mmosko/Zx50/boards/Zx50_MemoryCard_RevC1/.kinotes/KiNotes_Zx50_MemoryCard_RevC.md

# **Zx50_MemoryCard_RevC - Design Notes**

## **Overview**
<!-- Brief description of the PCB project -->

## **Schematic Notes**
<!-- Key circuit blocks, design rationale -->

## **Layout Considerations**
<!-- Layer stackup, impedance, keep-outs -->

## **Component Notes**
<!-- Click on designators like R1, C5, U3 to highlight on PCB -->

## **Power Distribution**
<!-- Power rails, decoupling strategy -->

## **Signal Integrity**
<!-- Critical nets, routing constraints -->

## **References**
<!-- Datasheets, application notes, calculations -->

---
*KiNotes - PCBtools.xyz*
