mmosko/Zx50/firmware/BusProbe_RevB/Zx50_Bus_Probe.X/STATUS.md

This is a perfect place to take a break. You have fought through some of the most notorious legacy bugs in the MPLAB X Simulator today and successfully built a robust, testable firmware architecture. 

Here is a summary of exactly where we are so you can jump right back in next time without missing a beat.

### 🌟 What is Working Perfectly
* **The Simulator Bypass:** We abandoned the buggy external SCL scripts in favor of a C-level `#ifdef __DEBUG` mock array in `UART_Read()`. This reliably instantly feeds your 5-byte packets (SYNC, OPCODE, ADDR_H, ADDR_L, PARAM) into the state machine.
* **The Command Router:** Your `while(1)` loop and `switch(opcode)` block in `main.c` perfectly parse the mock packets and route them to the correct functions.
* **Safe Boot State:** We updated `GPIO_Init()` to pre-load `LATA` and `LATB` to `1` (HIGH) before setting their `TRIS` directions. This ensures the Z80 control lines and transceiver Output Enables (`~OE`) boot up safely disabled (Ghost Mode) without glitching the bus.
* **Ghost/Unghost Logic:** The new `CMD_GHOST` (0x08) command and `Ghost()` function successfully toggle the data bus direction (`TRISD`) and transceiver `~OE` lines (`RA0`, `RA2`). You can see this clearly working in your latest Logic Analyzer trace.
* **UART ACKs:** We verified via the IO View that the hardware is correctly loading `0x5A` into `TXREG` and enabling the transmission shift register after every command.

### 🔍 Where to Resume Next Session
Looking at your final screenshot, `RA0` and `RA2` are correctly cycling, but **`RB0` (`~MREQ`) and `RB5` (`~WR`) are sitting flat at 5V** during the entire trace. 

Since we pre-loaded them to 5V in `hal.c`, they are behaving safely, but they aren't dropping low to actually strobe the Z80 bus during the `CMD_STORE` operation. 

**Your To-Do List for next time:**
1.  **Open `z80_bus.c`:** Check your `Z80_Mem_Write()` function. We need to ensure it is actually pulling `LATBbits.LATB0 = 0` and `LATBbits.LATB5 = 0`, holding them for a moment, and then returning them to `1`.
2.  **Test a Read Command:** Once the write strobes are fixed, we will change the mock array in `hal.c` to inject a `CMD_LD` (Memory Read) packet. This will let us verify that your Transceiver Direction pins (`RA1`, `RA3`) correctly flip to route data *inward* from the Z80 bus.
3.  **Physical Hardware:** Once those last few logic lines are verified, the firmware is fully simulated. You can switch to VS Code, flash the physical PIC, and hook up your logic analyzer to the real PCB!

Have a great break. Whenever you are ready to pick this back up, just say the word!
