mmosko/Zx50/boards/Zx50_Clock_Mezzanine/Zx50_Clock_Mezzanine.kicad_pcb

## KiCad design boards/legacy/Zx50_Clock_Mezzanine/Zx50_Clock_Mezzanine.kicad_pcb (2026-03-17, an earlier design)

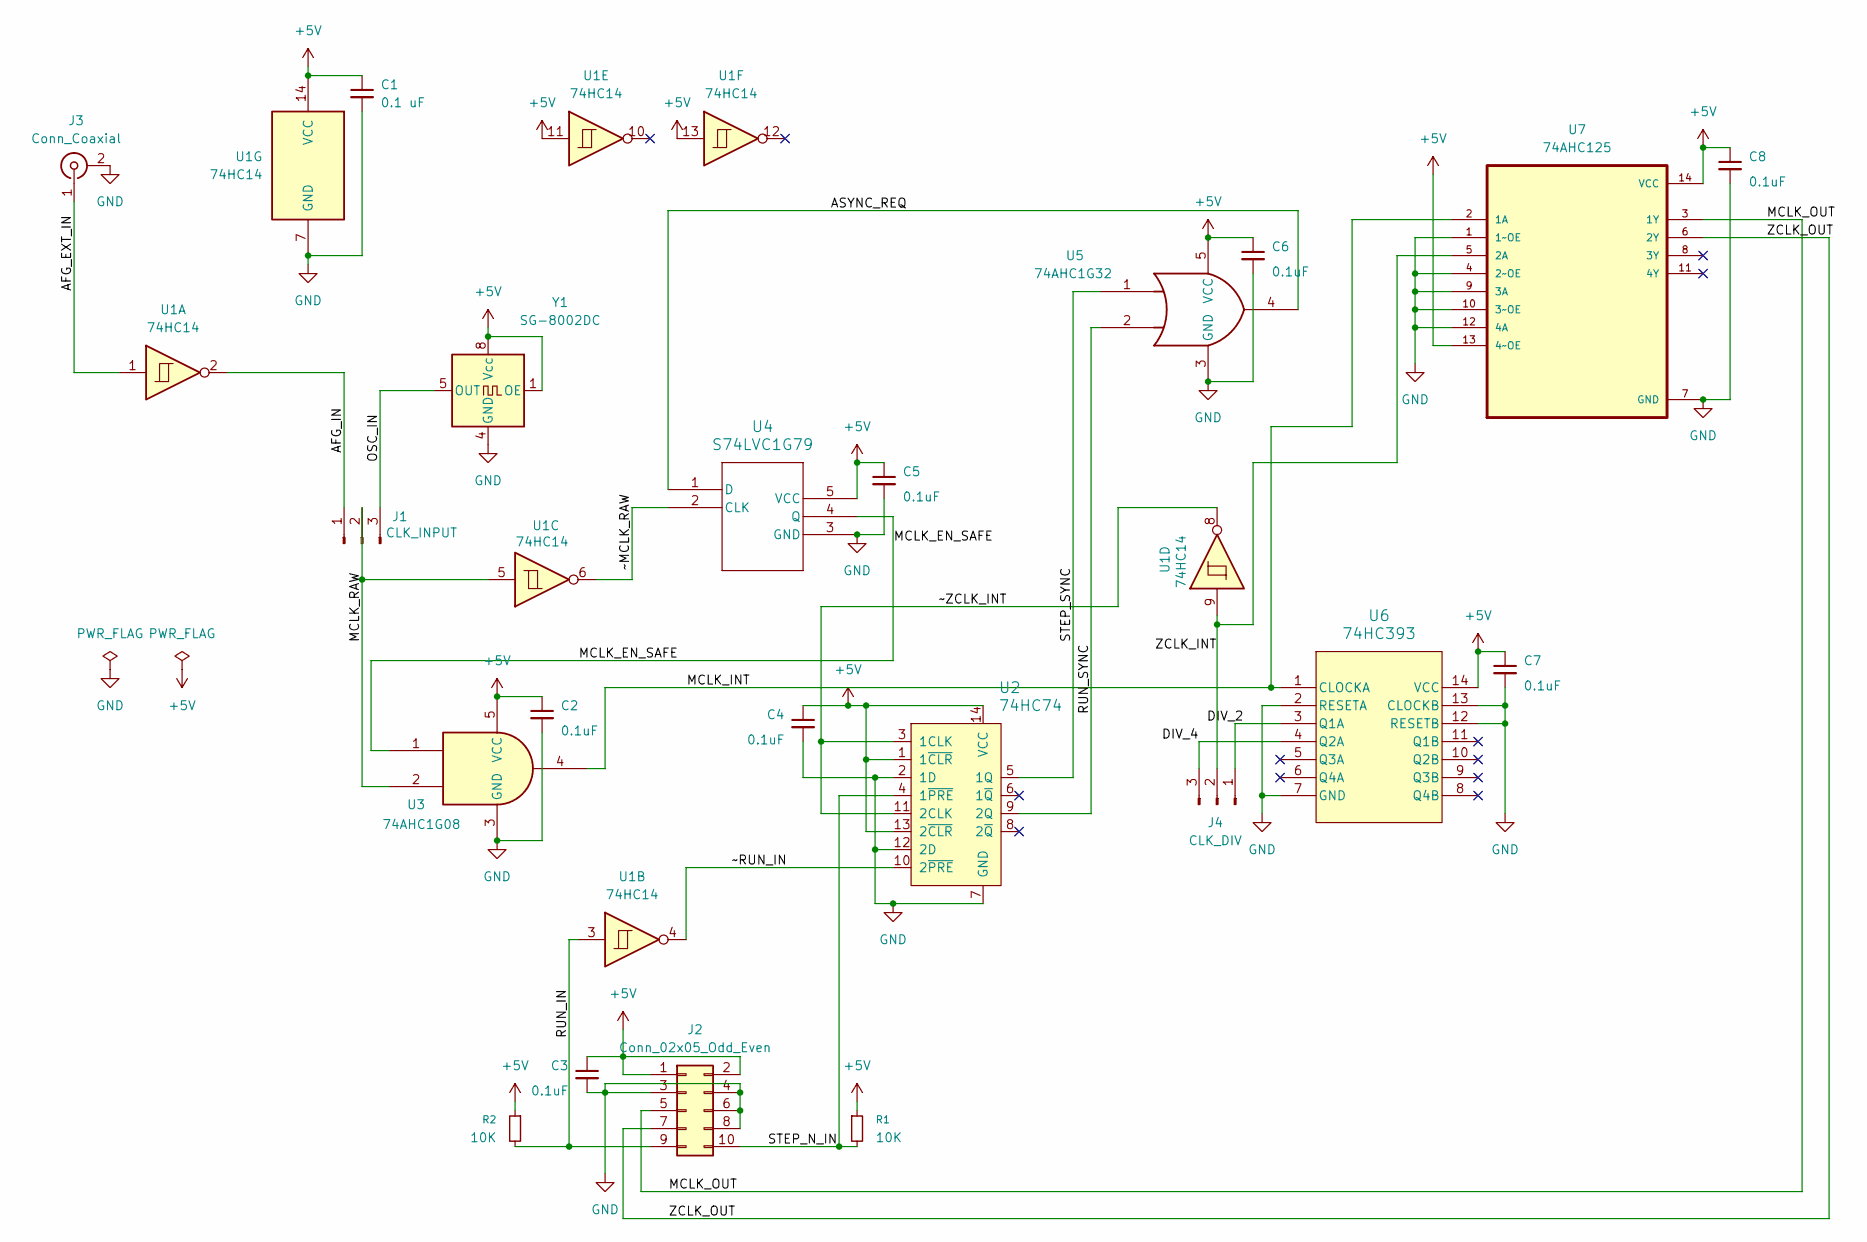
[picture p43: schematic Zx50_Clock_Mezzanine.kicad_sch]

Parts:
C1: 0.1 uF; C_0805_2012Metric_Pad1.18x1.45mm_HandSolder; DigiKey_PN 311-1140-1-ND
C2, C3, C4, C5, C6, C7, C8: 0.1uF; C_0805_2012Metric_Pad1.18x1.45mm_HandSolder; DigiKey_PN 311-1140-1-ND
J1: CLK_INPUT; PinHeader_1x03_P2.54mm_Vertical; DigiKey_PN 732-5316-ND
J2: Conn_02x05_Odd_Even; PinHeader_2x05_P2.54mm_Vertical; DigiKey_PN 2057-PH2RA-10-UA-ND
J3: Conn_Coaxial; BNC_Amphenol_B6252HB-NPP3G-50_Horizontal; DigiKey_PN ARF1178-ND
J4: CLK_DIV; PinHeader_1x03_P2.54mm_Vertical; DigiKey_PN 732-5316-ND
R1, R2: 10K; R_0805_2012Metric_Pad1.20x1.40mm_HandSolder; DigiKey_PN 311-10.0KCRCT-ND
U1: 74HC14; SOIC-14_3.9x8.7mm_P1.27mm; DigiKey_PN MC74HC14ADR2GOSCT-ND
U2: 74HC74; SOIC-14_3.9x8.7mm_P1.27mm; MPN SN74HC74N; Digi-Key_PN 296-1602-5-ND
U3: 74AHC1G08; SOT-23-5_HandSoldering; DigiKey_PN 296-1091-1-ND
U4: S74LVC1G79; SOT-23-5_HandSoldering; DigiKey_PN 296-9849-1-ND
U5: 74AHC1G32; SOT-23-5_HandSoldering; DigiKey_PN 296-1093-1-ND
U6: 74HC393; SOIC-14_3.9x8.7mm_P1.27mm; DigiKey_PN 296-8317-5-ND
U7: 74AHC125; SOIC-14_3.9x8.7mm_P1.27mm; DigiKey_PN 296-4530-1-ND
Y1: SG-8002DC; DIP-8_W7.62mm_Socket; DigiKey_PN 17-2485264-1-ND

Connections:
+5V: C1.1, C2.1, C3.1, C4.1, C5.1, C6.1, C7.1, C8.1, J2.1, J2.2, R1.1, R2.1, U1.11, U1.13, U1.14 (VCC), U2.1 (1~CLR), U2.13 (2~CLR), U2.14 (VCC), U3.5 (VCC), U4.5 (VCC), U5.5 (VCC), U6.14 (VCC), U7.13 (4~OE), U7.14 (VCC), Y1.1 (OE), Y1.8 (Vcc)
/AFG_EXT_IN: J3.1 (In), U1.1
/AFG_IN: J1.1, U1.2
/ASYNC_REQ: U4.1 (D), U5.4
/DIV_2: J4.1, U6.3 (Q1A)
/DIV_4: J4.3, U6.4 (Q2A)
/MCLK_EN_SAFE: U3.1, U4.4 (Q)
/MCLK_INT: U3.4, U6.1 (CLOCKA), U7.2 (1A)
/MCLK_OUT: J2.5, U7.3 (1Y)
/MCLK_RAW: J1.2, U1.5, U3.2
/OSC_IN: J1.3, Y1.5 (OUT)
/RUN_IN: J2.9, R2.2, U1.3
/RUN_SYNC: U2.9 (2Q), U5.2
/STEP_N_IN: J2.10, R1.2, U2.4 (1~PRE)
/STEP_SYNC: U2.5 (1Q), U5.1
/ZCLK_INT: J4.2, U1.9, U7.5 (2A)
/ZCLK_OUT: J2.7, U7.6 (2Y)
/~MCLK_RAW: U1.6, U4.2 (CLK)
/~RUN_IN: U1.4, U2.10 (2~PRE)
/~ZCLK_INT: U1.8, U2.3 (1CLK), U2.11 (2CLK)
GND: C1.2, C2.2, C3.2, C4.2, C5.2, C6.2, C7.2, C8.2, J2.3, J2.4, J2.6, J2.8, J3.2 (Ext), U1.7 (GND), U2.2 (1D), U2.7 (GND), U2.12 (2D), U3.3 (GND), U4.3 (GND), U5.3 (GND), U6.2 (RESETA), U6.7 (GND), U6.12 (RESETB), U6.13 (CLOCKB), U7.1 (1~OE), U7.4 (2~OE), U7.7 (GND), U7.9 (3A), U7.10 (3~OE), U7.12 (4A), Y1.4 (GND)

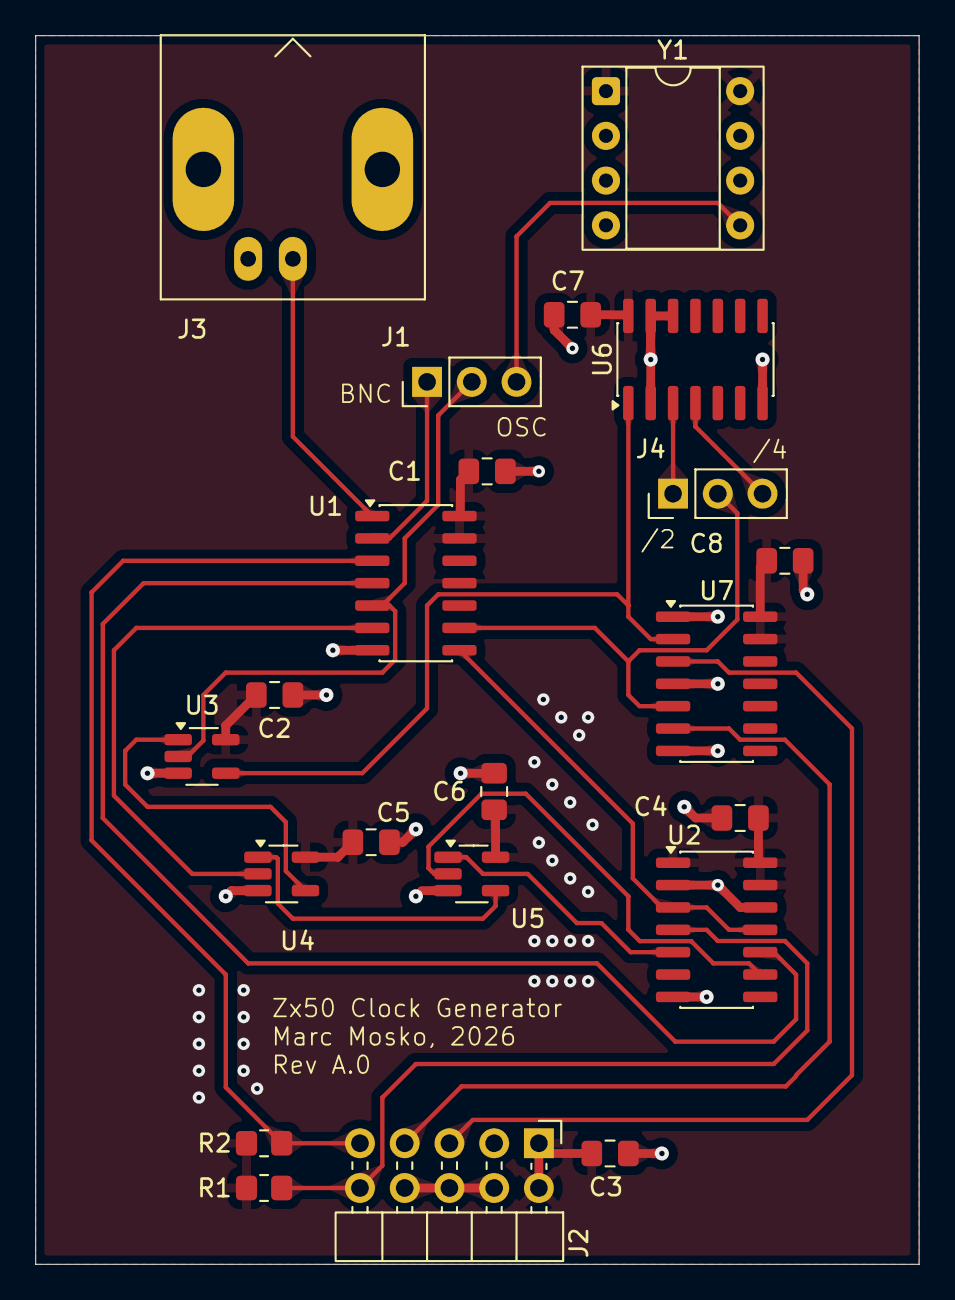
[picture p44: board Zx50_Clock_Mezzanine.kicad_pcb from above]

Board: 2 copper layers, 50.2 x 69.8 mm, 22 parts (0 on the bottom side), 21 nets.
