mmosko/Zx50/boards/Zx50_Backplane_RevD/Zx50_Backplane_RevD.kicad_pcb

## KiCad design boards/Zx50_Backplane_RevD/Zx50_Backplane_RevD.kicad_pcb (2026-05-28)

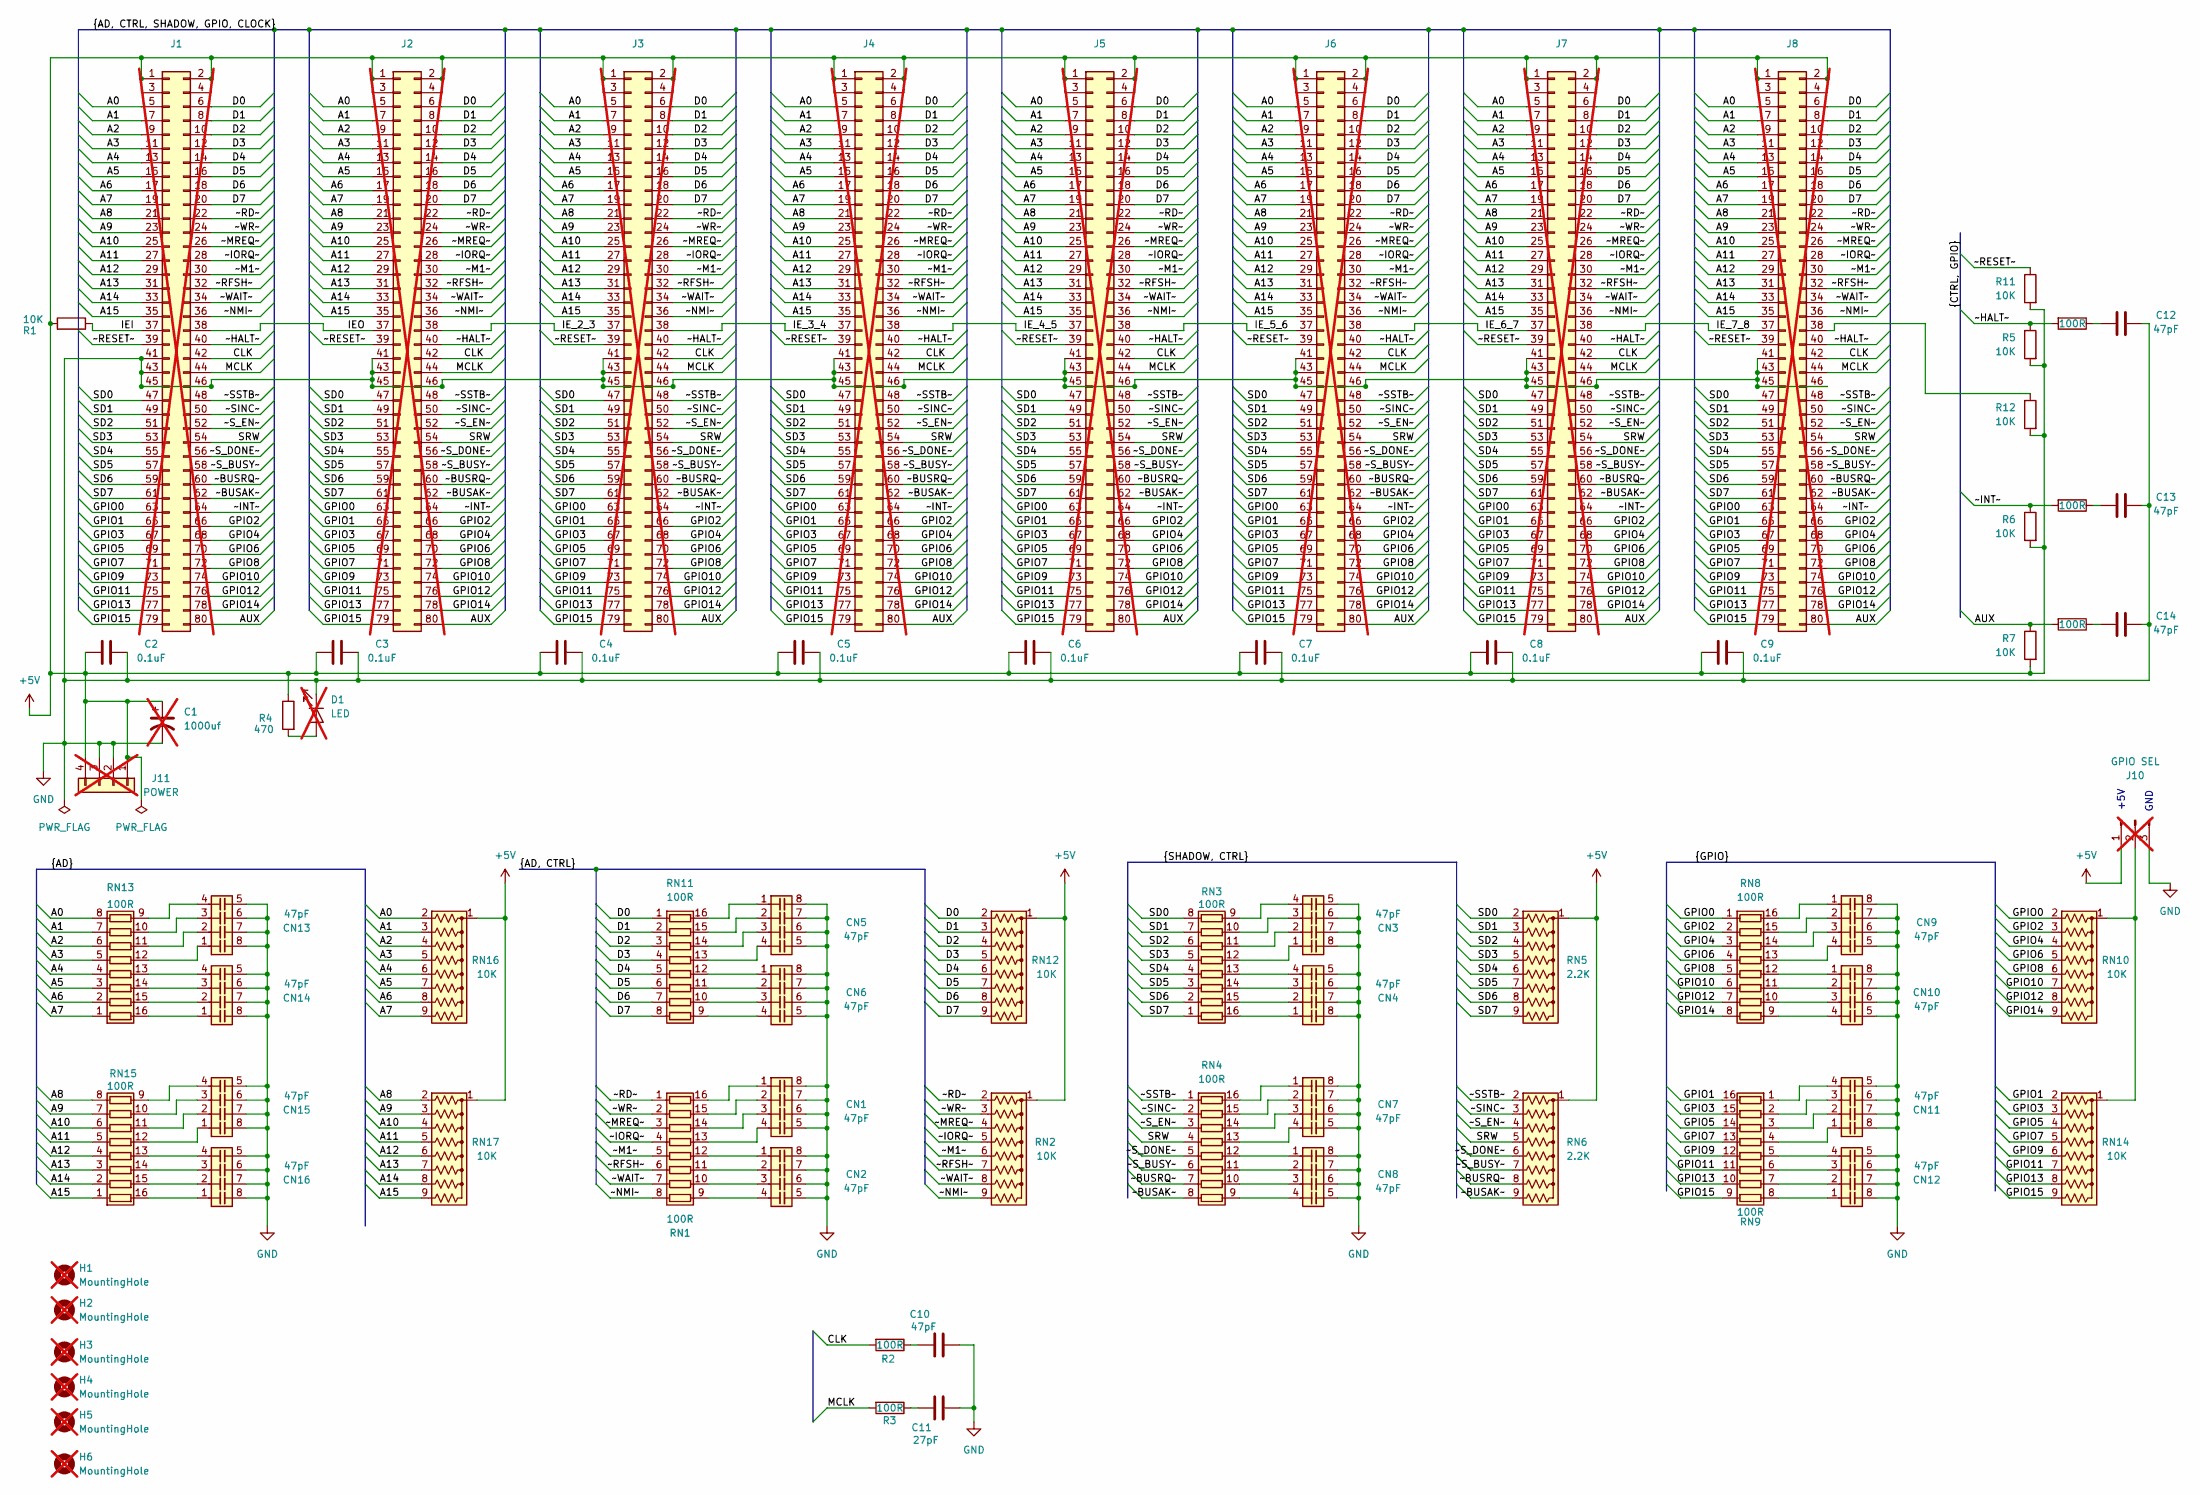
[picture p47: schematic Zx50_Backplane_RevD.kicad_sch]

Parts:
C1: 1000uf; CP_Radial_D10.0mm_P5.00mm; DigiKey_PN 493-15895-ND; not fitted
C2, C3, C4, C5, C6, C7, C8, C9: 0.1uF; C_0805_2012Metric; DigiKey_PN 399-C0805C104K5RACTUCT-ND
C10, C12, C13, C14: 47pF; C_0805_2012Metric; DigiKey_PN 399-C0805C101J5GACTUCT-ND
C11: 27pF; C_0805_2012Metric_Pad1.18x1.45mm_HandSolder; DigiKey_PN 478-600F270JT250XT4KCT-ND
CN1, CN2, CN3, CN4, CN5, CN6, CN7, CN8, CN9, CN10, CN11, CN12, CN13, CN14, CN15, CN16: 47pF; CAP_CA0612_3P2X1P6_YAG; DigiKey_PN 13-CA0612JRNPO9BN470CT-ND
D1: LED; LED_D5.0mm; DigiKey_PN 732-5016-ND; not fitted
H1, H2, H3, H4, H5, H6: MountingHole; MountingHole_3.2mm_M3; DigiKey_PN SJ5003-0-ND; not fitted
J1, J2, J3, J4, J5, J6, J7, J8: Conn_02x40_Odd_Even; PinSocket_2x40_P2.54mm_Vertical_Oval; DigiKey_PN SAM1179-40-ND; not fitted
J10: GPIO SEL; PinHeader_1x03_P2.54mm_Vertical; DigiKey_PN 732-5316-ND; not fitted
J11: POWER; TerminalBlock_Phoenix_MKDS-1,5-4-5.08_1x04_P5.08mm_Horizont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; DigiKey_PN 277-1238-ND; not fitted
R1, R5, R6, R7, R11, R12: 10K; R_0805_2012Metric_Pad1.20x1.40mm_HandSolder; DigiKey_PN RMCF0805FT10K0CT-ND
R2, R3, R8, R9, R10: 100R; R_0805_2012Metric; DigiKey_PN 311-100CRCT-ND
R4: 470; R_0805_2012Metric_Pad1.20x1.40mm_HandSolder; DigiKey_PN A130132CT-ND
RN1, RN3, RN4, RN8, RN9, RN11, RN13, RN15: 100R; SOIC-16W_5.3x10.2mm_P1.27mm; DigiKey_PN 4816P-1-101LFCT-ND
RN2, RN10, RN12, RN14, RN16, RN17: 10K; RN_9SRT_1_27mm_handsolder; DigiKey_PN 60-752091103GPTR7CT-ND
RN5, RN6: 2.2K; RN_9SRT_1_27mm_handsolder; DigiKey_PN 60-752091222GPTR7CT-ND

Connections:
+5V: C1.1, C2.1, C3.1, C4.1, C5.1, C6.1, C7.1, C8.1, C9.1, J1.1, J1.2, J1.3, J1.4, J2.1, J2.2, J2.3, J2.4, J3.1, J3.2, J3.3, J3.4, J4.1, J4.2, J4.3, J4.4, J5.1, J5.2, J5.3, J5.4, J6.1, J6.2, J6.3, J6.4, J7.1, J7.2, J7.3, J7.4, J8.1, J8.2, J8.3, J8.4, J10.1, J11.1, J11.4, R1.2, R4.1, R5.2, R6.2, R7.2, R11.2, R12.2, RN2.1 (common), RN5.1 (common), RN6.1 (common), RN12.1 (common), RN16.1 (common), RN17.1 (common)
/A0: J1.5, J2.5, J3.5, J4.5, J5.5, J6.5, J7.5, J8.5, RN13.8 (R8.1), RN16.2 (R1)
/A1: J1.7, J2.7, J3.7, J4.7, J5.7, J6.7, J7.7, J8.7, RN13.7 (R7.1), RN16.3 (R2)
/A2: J1.9, J2.9, J3.9, J4.9, J5.9, J6.9, J7.9, J8.9, RN13.6 (R6.1), RN16.4 (R3)
/A3: J1.11, J2.11, J3.11, J4.11, J5.11, J6.11, J7.11, J8.11, RN13.5 (R5.1), RN16.5 (R4)
/A4: J1.13, J2.13, J3.13, J4.13, J5.13, J6.13, J7.13, J8.13, RN13.4 (R4.1), RN16.6 (R5)
/A5: J1.15, J2.15, J3.15, J4.15, J5.15, J6.15, J7.15, J8.15, RN13.3 (R3.1), RN16.7 (R6)
/A6: J1.17, J2.17, J3.17, J4.17, J5.17, J6.17, J7.17, J8.17, RN13.2 (R2.1), RN16.8 (R7)
/A7: J1.19, J2.19, J3.19, J4.19, J5.19, J6.19, J7.19, J8.19, RN13.1 (R1.1), RN16.9 (R8)
/A8: J1.21, J2.21, J3.21, J4.21, J5.21, J6.21, J7.21, J8.21, RN15.8 (R8.1), RN17.2 (R1)
/A9: J1.23, J2.23, J3.23, J4.23, J5.23, J6.23, J7.23, J8.23, RN15.7 (R7.1), RN17.3 (R2)
/A10: J1.25, J2.25, J3.25, J4.25, J5.25, J6.25, J7.25, J8.25, RN15.6 (R6.1), RN17.4 (R3)
/A11: J1.27, J2.27, J3.27, J4.27, J5.27, J6.27, J7.27, J8.27, RN15.5 (R5.1), RN17.5 (R4)
/A12: J1.29, J2.29, J3.29, J4.29, J5.29, J6.29, J7.29, J8.29, RN15.4 (R4.1), RN17.6 (R5)
/A13: J1.31, J2.31, J3.31, J4.31, J5.31, J6.31, J7.31, J8.31, RN15.3 (R3.1), RN17.7 (R6)
/A14: J1.33, J2.33, J3.33, J4.33, J5.33, J6.33, J7.33, J8.33, RN15.2 (R2.1), RN17.8 (R7)
/A15: J1.35, J2.35, J3.35, J4.35, J5.35, J6.35, J7.35, J8.35, RN15.1 (R1.1), RN17.9 (R8)
/AUX: J1.80, J2.80, J3.80, J4.80, J5.80, J6.80, J7.80, J8.80, R7.1, R10.1
/CLK: J1.42, J2.42, J3.42, J4.42, J5.42, J6.42, J7.42, J8.42, R2.1
/D0: J1.6, J2.6, J3.6, J4.6, J5.6, J6.6, J7.6, J8.6, RN11.1 (R1.1), RN12.2 (R1)
/D1: J1.8, J2.8, J3.8, J4.8, J5.8, J6.8, J7.8, J8.8, RN11.2 (R2.1), RN12.3 (R2)
/D2: J1.10, J2.10, J3.10, J4.10, J5.10, J6.10, J7.10, J8.10, RN11.3 (R3.1), RN12.4 (R3)
/D3: J1.12, J2.12, J3.12, J4.12, J5.12, J6.12, J7.12, J8.12, RN11.4 (R4.1), RN12.5 (R4)
/D4: J1.14, J2.14, J3.14, J4.14, J5.14, J6.14, J7.14, J8.14, RN11.5 (R5.1), RN12.6 (R5)
/D5: J1.16, J2.16, J3.16, J4.16, J5.16, J6.16, J7.16, J8.16, RN11.6 (R6.1), RN12.7 (R6)
/D6: J1.18, J2.18, J3.18, J4.18, J5.18, J6.18, J7.18, J8.18, RN11.7 (R7.1), RN12.8 (R7)
/D7: J1.20, J2.20, J3.20, J4.20, J5.20, J6.20, J7.20, J8.20, RN11.8 (R8.1), RN12.9 (R8)
/GPIO0: J1.63, J2.63, J3.63, J4.63, J5.63, J6.63, J7.63, J8.63, RN8.1 (R1.1), RN10.2 (R1)
/GPIO1: J1.65, J2.65, J3.65, J4.65, J5.65, J6.65, J7.65, J8.65, RN9.16 (R1.2), RN14.2 (R1)
/GPIO2: J1.66, J2.66, J3.66, J4.66, J5.66, J6.66, J7.66, J8.66, RN8.2 (R2.1), RN10.3 (R2)
/GPIO3: J1.67, J2.67, J3.67, J4.67, J5.67, J6.67, J7.67, J8.67, RN9.15 (R2.2), RN14.3 (R2)
/GPIO4: J1.68, J2.68, J3.68, J4.68, J5.68, J6.68, J7.68, J8.68, RN8.3 (R3.1), RN10.4 (R3)
/GPIO5: J1.69, J2.69, J3.69, J4.69, J5.69, J6.69, J7.69, J8.69, RN9.14 (R3.2), RN14.4 (R3)
/GPIO6: J1.70, J2.70, J3.70, J4.70, J5.70, J6.70, J7.70, J8.70, RN8.4 (R4.1), RN10.5 (R4)
/GPIO7: J1.71, J2.71, J3.71, J4.71, J5.71, J6.71, J7.71, J8.71, RN9.13 (R4.2), RN14.5 (R4)
/GPIO8: J1.72, J2.72, J3.72, J4.72, J5.72, J6.72, J7.72, J8.72, RN8.5 (R5.1), RN10.6 (R5)
/GPIO9: J1.73, J2.73, J3.73, J4.73, J5.73, J6.73, J7.73, J8.73, RN9.12 (R5.2), RN14.6 (R5)
/GPIO10: J1.74, J2.74, J3.74, J4.74, J5.74, J6.74, J7.74, J8.74, RN8.6 (R6.1), RN10.7 (R6)
/GPIO11: J1.75, J2.75, J3.75, J4.75, J5.75, J6.75, J7.75, J8.75, RN9.11 (R6.2), RN14.7 (R6)
/GPIO12: J1.76, J2.76, J3.76, J4.76, J5.76, J6.76, J7.76, J8.76, RN8.7 (R7.1), RN10.8 (R7)
/GPIO13: J1.77, J2.77, J3.77, J4.77, J5.77, J6.77, J7.77, J8.77, RN9.10 (R7.2), RN14.8 (R7)
/GPIO14: J1.78, J2.78, J3.78, J4.78, J5.78, J6.78, J7.78, J8.78, RN8.8 (R8.1), RN10.9 (R8)
/GPIO15: J1.79, J2.79, J3.79, J4.79, J5.79, J6.79, J7.79, J8.79, RN9.9 (R8.2), RN14.9 (R8)
/IEI: J1.37, R1.1
/IEO: J1.38, J2.37
/IE_2_3: J2.38, J3.37
/IE_3_4: J3.38, J4.37
/IE_4_5: J4.38, J5.37
/IE_5_6: J5.38, J6.37
/IE_6_7: J6.38, J7.37
/IE_7_8: J7.38, J8.37
/MCLK: J1.44, J2.44, J3.44, J4.44, J5.44, J6.44, J7.44, J8.44, R3.1
/SD0: J1.47, J2.47, J3.47, J4.47, J5.47, J6.47, J7.47, J8.47, RN3.8 (R8.1), RN5.2 (R1)
/SD1: J1.49, J2.49, J3.49, J4.49, J5.49, J6.49, J7.49, J8.49, RN3.7 (R7.1), RN5.3 (R2)
/SD2: J1.51, J2.51, J3.51, J4.51, J5.51, J6.51, J7.51, J8.51, RN3.6 (R6.1), RN5.4 (R3)
/SD3: J1.53, J2.53, J3.53, J4.53, J5.53, J6.53, J7.53, J8.53, RN3.5 (R5.1), RN5.5 (R4)
/SD4: J1.55, J2.55, J3.55, J4.55, J5.55, J6.55, J7.55, J8.55, RN3.4 (R4.1), RN5.6 (R5)
/SD5: J1.57, J2.57, J3.57, J4.57, J5.57, J6.57, J7.57, J8.57, RN3.3 (R3.1), RN5.7 (R6)
/SD6: J1.59, J2.59, J3.59, J4.59, J5.59, J6.59, J7.59, J8.59, RN3.2 (R2.1), RN5.8 (R7)
/SD7: J1.61, J2.61, J3.61, J4.61, J5.61, J6.61, J7.61, J8.61, RN3.1 (R1.1), RN5.9 (R8)
/SRW: J1.54, J2.54, J3.54, J4.54, J5.54, J6.54, J7.54, J8.54, RN4.4 (R4.1), RN6.5 (R4)
/~BUSAK~: J1.62, J2.62, J3.62, J4.62, J5.62, J6.62, J7.62, J8.62, RN4.8 (R8.1), RN6.9 (R8)
/~BUSRQ~: J1.60, J2.60, J3.60, J4.60, J5.60, J6.60, J7.60, J8.60, RN4.7 (R7.1), RN6.8 (R7)
/~HALT~: J1.40, J2.40, J3.40, J4.40, J5.40, J6.40, J7.40, J8.40, R5.1, R8.1
/~INT~: J1.64, J2.64, J3.64, J4.64, J5.64, J6.64, J7.64, J8.64, R6.1, R9.1
/~IORQ~: J1.28, J2.28, J3.28, J4.28, J5.28, J6.28, J7.28, J8.28, RN1.4 (R4.1), RN2.5 (R4)
/~M1~: J1.30, J2.30, J3.30, J4.30, J5.30, J6.30, J7.30, J8.30, RN1.5 (R5.1), RN2.6 (R5)
/~MREQ~: J1.26, J2.26, J3.26, J4.26, J5.26, J6.26, J7.26, J8.26, RN1.3 (R3.1), RN2.4 (R3)
/~NMI~: J1.36, J2.36, J3.36, J4.36, J5.36, J6.36, J7.36, J8.36, RN1.8 (R8.1), RN2.9 (R8)
/~RD~: J1.22, J2.22, J3.22, J4.22, J5.22, J6.22, J7.22, J8.22, RN1.1 (R1.1), RN2.2 (R1)
/~RESET~: J1.39, J2.39, J3.39, J4.39, J5.39, J6.39, J7.39, J8.39, R11.1
/~RFSH~: J1.32, J2.32, J3.32, J4.32, J5.32, J6.32, J7.32, J8.32, RN1.6 (R6.1), RN2.7 (R6)
/~SINC~: J1.50, J2.50, J3.50, J4.50, J5.50, J6.50, J7.50, J8.50, RN4.2 (R2.1), RN6.3 (R2)
/~SSTB~: J1.48, J2.48, J3.48, J4.48, J5.48, J6.48, J7.48, J8.48, RN4.1 (R1.1), RN6.2 (R1)
/~S_BUSY~: J1.58, J2.58, J3.58, J4.58, J5.58, J6.58, J7.58, J8.58, RN4.6 (R6.1), RN6.7 (R6)
/~S_DONE~: J1.56, J2.56, J3.56, J4.56, J5.56, J6.56, J7.56, J8.56, RN4.5 (R5.1), RN6.6 (R5)
/~S_EN~: J1.52, J2.52, J3.52, J4.52, J5.52, J6.52, J7.52, J8.52, RN4.3 (R3.1), RN6.4 (R3)
/~WAIT~: J1.34, J2.34, J3.34, J4.34, J5.34, J6.34, J7.34, J8.34, RN1.7 (R7.1), RN2.8 (R7)
/~WR~: J1.24, J2.24, J3.24, J4.24, J5.24, J6.24, J7.24, J8.24, RN1.2 (R2.1), RN2.3 (R2)
GND: C1.2, C2.2, C3.2, C4.2, C5.2, C6.2, C7.2, C8.2, C9.2, C10.2, C11.1, C12.2, C13.2, C14.2, CN1.5 (C4), CN1.6 (C3), CN1.7 (C2), CN1.8 (C1), CN2.5 (C4), CN2.6 (C3), CN2.7 (C2), CN2.8 (C1), CN3.5 (C4), CN3.6 (C3), CN3.7 (C2), CN3.8 (C1), CN4.5 (C4), CN4.6 (C3), CN4.7 (C2), CN4.8 (C1), CN5.5 (C4), CN5.6 (C3), CN5.7 (C2), CN5.8 (C1), CN6.5 (C4), CN6.6 (C3), CN6.7 (C2), CN6.8 (C1), CN7.5 (C4), CN7.6 (C3), CN7.7 (C2), CN7.8 (C1), CN8.5 (C4), CN8.6 (C3), CN8.7 (C2), CN8.8 (C1), CN9.5 (C4), CN9.6 (C3), CN9.7 (C2), CN9.8 (C1), CN10.5 (C4), CN10.6 (C3), CN10.7 (C2), CN10.8 (C1), CN11.5 (C4), CN11.6 (C3), CN11.7 (C2), CN11.8 (C1), CN12.5 (C4), CN12.6 (C3), CN12.7 (C2), CN12.8 (C1), CN13.5 (C4), CN13.6 (C3), CN13.7 (C2), CN13.8 (C1), CN14.5 (C4), CN14.6 (C3), CN14.7 (C2), CN14.8 (C1), CN15.5 (C4), CN15.6 (C3), CN15.7 (C2), CN15.8 (C1), CN16.5 (C4), CN16.6 (C3), CN16.7 (C2), CN16.8 (C1), D1.1 (K), J1.41, J1.43, J1.45, J1.46, J2.41, J2.43, J2.45, J2.46, J3.41, J3.43, J3.45, J3.46, J4.41, J4.43, J4.45, J4.46, J5.41, J5.43, J5.45, J5.46, J6.41, J6.43, J6.45, J6.46, J7.41, J7.43, J7.45, J7.46, J8.41, J8.43, J8.45, J8.46, J10.3, J11.2, J11.3
unnamed: C10.1, R2.2
unnamed: C11.2, R3.2
unnamed: C12.1, R8.2
unnamed: C13.1, R9.2
unnamed: C14.1, R10.2
unnamed: D1.2 (A), R4.2
unnamed: J8.38, R12.1
unnamed: J10.2, RN10.1 (common), RN14.1 (common)
unnamed: CN1.1 (common), RN1.16 (R1.2)
unnamed: CN1.2 (common), RN1.15 (R2.2)
unnamed: CN1.3 (common), RN1.14 (R3.2)
unnamed: CN1.4 (common), RN1.13 (R4.2)
unnamed: CN2.1 (common), RN1.12 (R5.2)
unnamed: CN2.2 (common), RN1.11 (R6.2)
unnamed: CN2.3 (common), RN1.10 (R7.2)
unnamed: CN2.4 (common), RN1.9 (R8.2)
unnamed: CN4.1 (common), RN3.16 (R1.2)
unnamed: CN4.2 (common), RN3.15 (R2.2)
unnamed: CN4.3 (common), RN3.14 (R3.2)
unnamed: CN4.4 (common), RN3.13 (R4.2)
unnamed: CN3.1 (common), RN3.12 (R5.2)
unnamed: CN3.2 (common), RN3.11 (R6.2)
unnamed: CN3.3 (common), RN3.10 (R7.2)
unnamed: CN3.4 (common), RN3.9 (R8.2)
unnamed: CN7.1 (common), RN4.16 (R1.2)
unnamed: CN7.2 (common), RN4.15 (R2.2)
unnamed: CN7.3 (common), RN4.14 (R3.2)
unnamed: CN7.4 (common), RN4.13 (R4.2)
unnamed: CN8.1 (common), RN4.12 (R5.2)
unnamed: CN8.2 (common), RN4.11 (R6.2)
unnamed: CN8.3 (common), RN4.10 (R7.2)
unnamed: CN8.4 (common), RN4.9 (R8.2)
unnamed: CN9.1 (common), RN8.16 (R1.2)
unnamed: CN9.2 (common), RN8.15 (R2.2)
unnamed: CN9.3 (common), RN8.14 (R3.2)
unnamed: CN9.4 (common), RN8.13 (R4.2)
unnamed: CN10.1 (common), RN8.12 (R5.2)
unnamed: CN10.2 (common), RN8.11 (R6.2)
unnamed: CN10.3 (common), RN8.10 (R7.2)
unnamed: CN10.4 (common), RN8.9 (R8.2)
unnamed: CN11.4 (common), RN9.1 (R1.1)
unnamed: CN11.3 (common), RN9.2 (R2.1)
unnamed: CN11.2 (common), RN9.3 (R3.1)
unnamed: CN11.1 (common), RN9.4 (R4.1)
unnamed: CN12.4 (common), RN9.5 (R5.1)
unnamed: CN12.3 (common), RN9.6 (R6.1)
unnamed: CN12.2 (common), RN9.7 (R7.1)
unnamed: CN12.1 (common), RN9.8 (R8.1)
unnamed: CN5.1 (common), RN11.16 (R1.2)
unnamed: CN5.2 (common), RN11.15 (R2.2)
unnamed: CN5.3 (common), RN11.14 (R3.2)
unnamed: CN5.4 (common), RN11.13 (R4.2)
unnamed: CN6.1 (common), RN11.12 (R5.2)
unnamed: CN6.2 (common), RN11.11 (R6.2)
unnamed: CN6.3 (common), RN11.10 (R7.2)
unnamed: CN6.4 (common), RN11.9 (R8.2)
unnamed: CN14.1 (common), RN13.16 (R1.2)
unnamed: CN14.2 (common), RN13.15 (R2.2)
unnamed: CN14.3 (common), RN13.14 (R3.2)
unnamed: CN14.4 (common), RN13.13 (R4.2)
unnamed: CN13.1 (common), RN13.12 (R5.2)
unnamed: CN13.2 (common), RN13.11 (R6.2)
unnamed: CN13.3 (common), RN13.10 (R7.2)
unnamed: CN13.4 (common), RN13.9 (R8.2)
unnamed: CN16.1 (common), RN15.16 (R1.2)
unnamed: CN16.2 (common), RN15.15 (R2.2)
unnamed: CN16.3 (common), RN15.14 (R3.2)
unnamed: CN16.4 (common), RN15.13 (R4.2)
unnamed: CN15.1 (common), RN15.12 (R5.2)
unnamed: CN15.2 (common), RN15.11 (R6.2)
unnamed: CN15.3 (common), RN15.10 (R7.2)
unnamed: CN15.4 (common), RN15.9 (R8.2)

Notes on the sheet:
+5V
GND

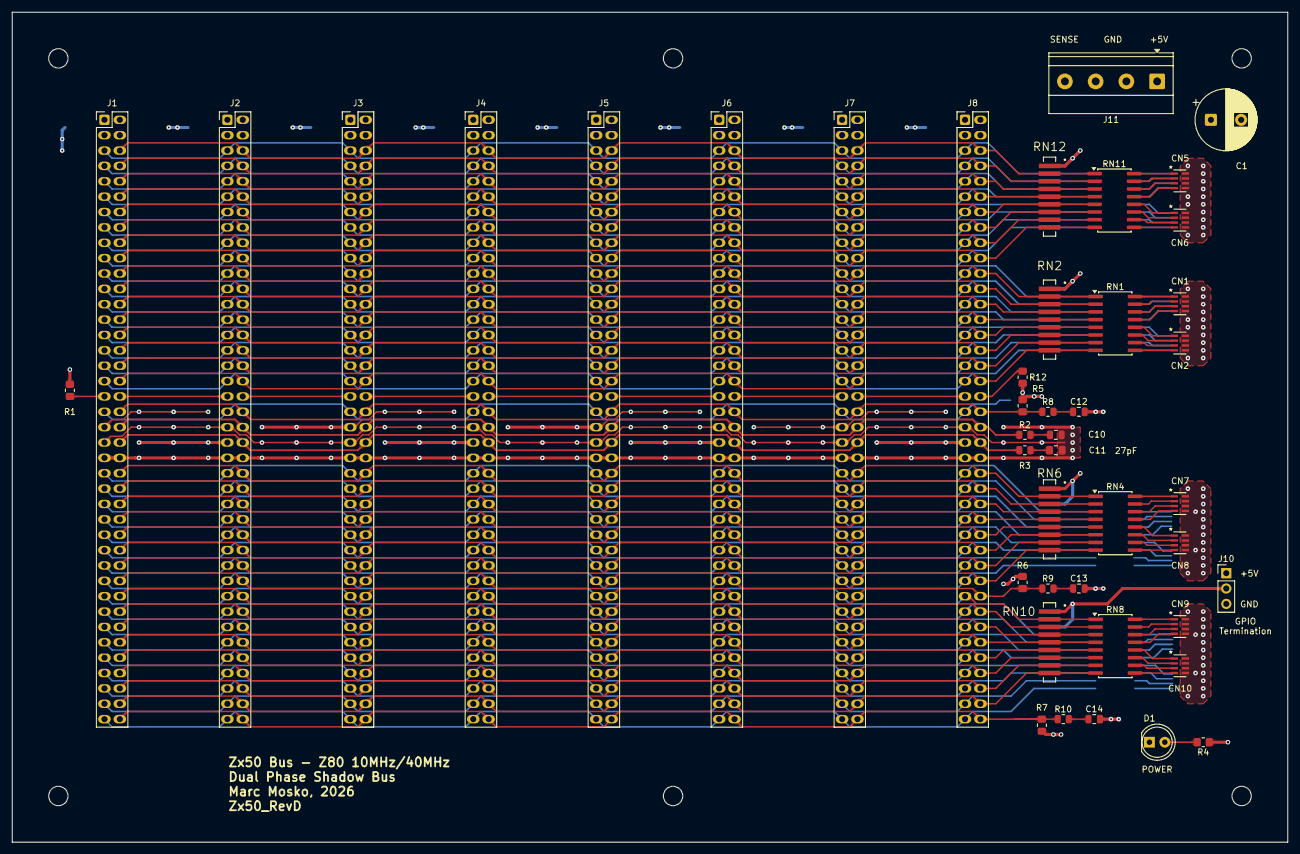
[picture p48: board Zx50_Backplane_RevD.kicad_pcb from above]

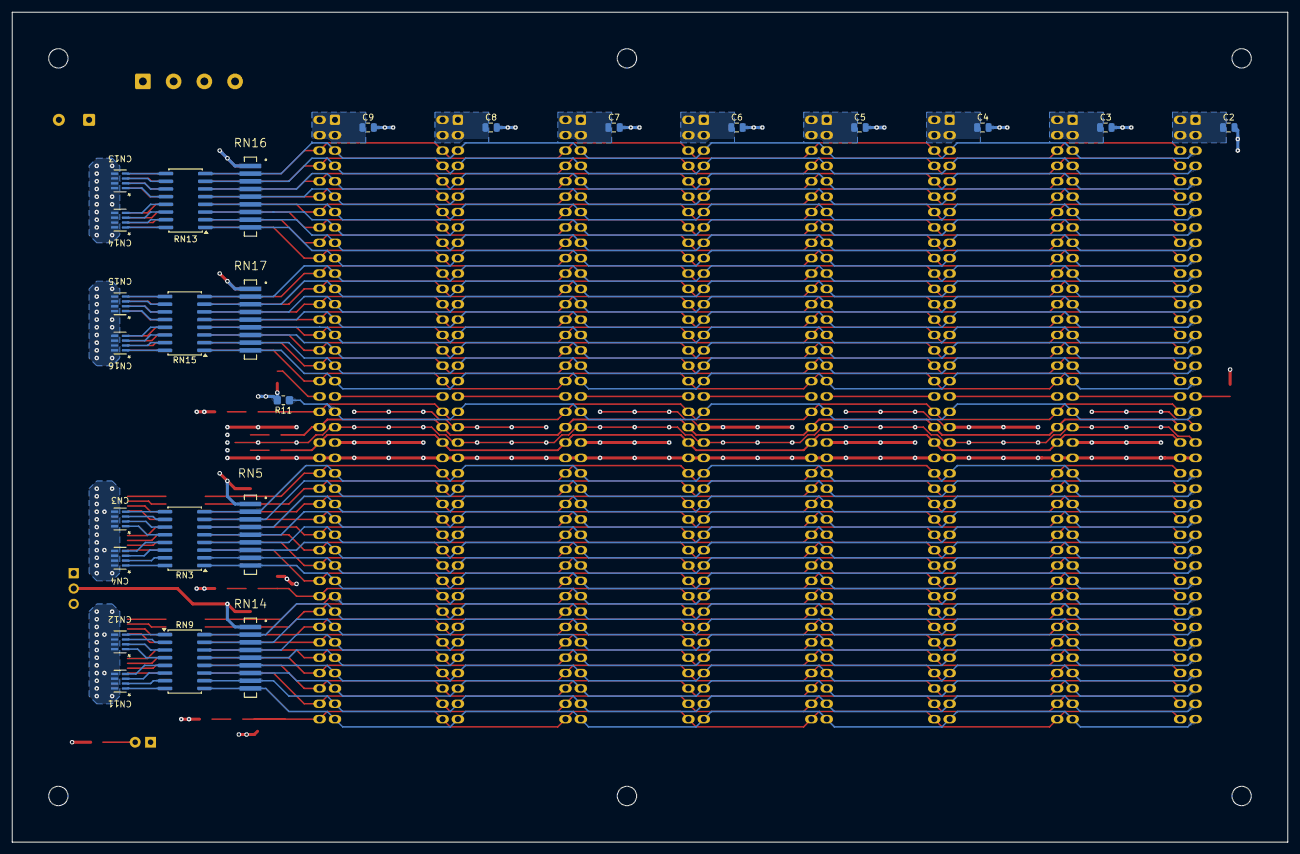
[picture p49: board Zx50_Backplane_RevD.kicad_pcb from below]

Board: 4 copper layers, 210.8 x 137.2 mm, 75 parts (25 on the bottom side), 152 nets.
