mmosko/Zx50/boards/Zx50_Clock_Mezzanine_RevC/Zx50_Clock_Mezzanine_RevC.kicad_pcb

## KiCad design boards/Zx50_Clock_Mezzanine_RevC/Zx50_Clock_Mezzanine_RevC.kicad_pcb (2026-05-21)

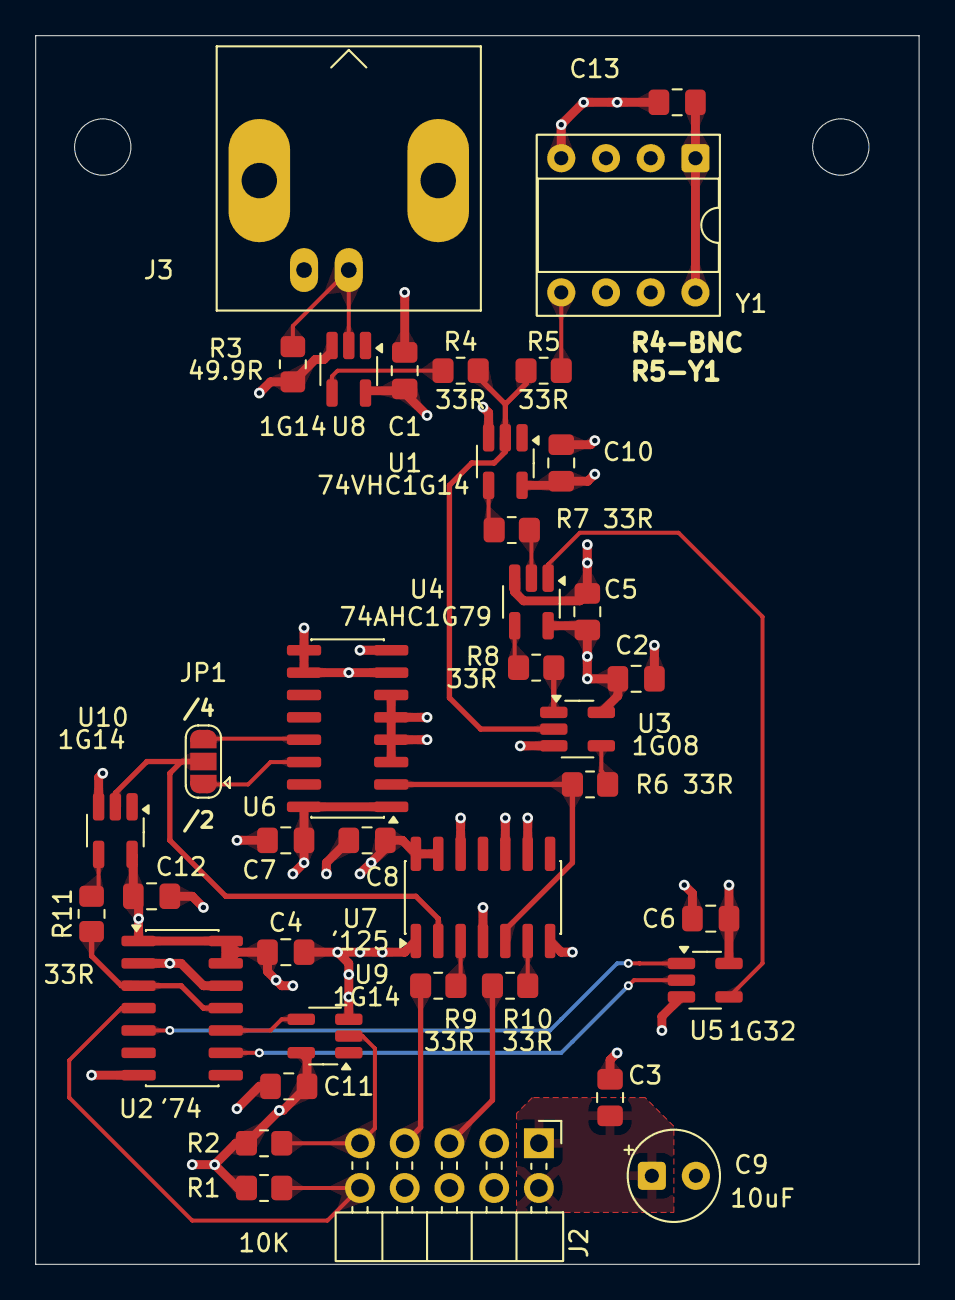
[picture p50: board Zx50_Clock_Mezzanine_RevC.kicad_pcb from above]

Board: 4 copper layers, 50.2 x 69.8 mm, 38 parts (0 on the bottom side), 27 nets.

Parts:
C1, C10, C11, C12, C13: 0.1 uF; C_0805_2012Metric_Pad1.18x1.45mm_HandSolder
C2, C3, C4, C5, C6, C7, C8: 0.1uF; C_0805_2012Metric_Pad1.18x1.45mm_HandSolder
C9: 10uF; CP_Radial_Tantal_D5.0mm_P2.50mm
J2: Conn_02x05_Odd_Even; PinHeader_2x05_P2.54mm_Horizontal_Edge
J3: Conn_Coaxial; BNC_Amphenol_B6252HB-NPP3G-50_Horizontal
JP1: CLOCK DIV; SolderJumper-3_P1.3mm_Open_RoundedPad1.0x1.5mm
R1, R2: 10K; R_0805_2012Metric_Pad1.20x1.40mm_HandSolder
R3: 49.9R; R_0805_2012Metric_Pad1.20x1.40mm_HandSolder
R4, R5, R6, R7, R8, R9, R10, R11: 33R; R_0805_2012Metric_Pad1.20x1.40mm_HandSolder
U1: 74VHC1G14; SOT-23-5_HandSoldering
U2: '74; SOIC-14_3.9x8.7mm_P1.27mm
U3: 1G08; SOT-23-5_HandSoldering
U4: 74AHC1G79; SOT-23-5_HandSoldering
U5: 1G32; SOT-23-5_HandSoldering
U6: CD74AC161M96; SOIC-16_3.9x9.9mm_P1.27mm
U7: '125; SOIC-14_3.9x8.7mm_P1.27mm
U8, U9, U10: 1G14; SOT-23-5_HandSoldering
Y1: SG-8002DC; DIP-8_W7.62mm_Socket

Connections:
+5V: C1.1, C2.1, C3.1, C4.1, C5.1, C6.1, C7.1, C8.1, C9.1, C10.1, C11.1, C12.1, C13.1, J2.1, J2.2, R1.1, R2.1, U1.5 (VCC), U2.1 (1~CLR), U2.13 (2~CLR), U2.14 (VCC), U3.5 (VCC), U4.5 (VCC), U5.5 (VCC), U6.1 (~CLR), U6.7 (ENP), U6.9 (~LOAD), U6.10 (ENT), U6.16 (VCC), U7.13 (4~OE), U7.14 (VCC), U8.5 (VCC), U9.5 (VCC), U10.5 (VCC), Y1.1 (OE), Y1.8 (Vcc)
/AFG_EXT_IN: J3.1 (In), R3.1, U8.2 (IN_A)
/ASYNC_REQ: U4.1 (D), U5.4
/DIV_2: JP1.1 (A), U6.14 (QA)
/DIV_4: JP1.3 (B), U6.13 (QB)
/MCLK_EN_SAFE: R8.1, U3.1
/MCLK_INT: R6.2, U6.2 (CLK), U7.5 (2A)
/MCLK_OUT: J2.5, R10.2
/MCLK_RAW: R4.2, R5.1, U1.2 (IN_A), U3.2
/RUN_IN: J2.9, R2.2, U9.2 (IN_A)
/RUN_SYNC: U2.9 (2Q), U5.2
/STEP_N_IN: J2.10, R1.2, U2.4 (1~PRE)
/STEP_SYNC: U2.5 (1Q), U5.1
/ZCLK_INT: JP1.2 (C), U7.2 (1A), U10.2 (IN_A)
/ZCLK_OUT: J2.7, R9.2
/~MCLK_RAW: R7.2, U4.2 (CLK)
/~RUN_IN: U2.10 (2~PRE), U9.4 (OUT~Y)
/~ZCLK_INT: R11.1, U2.3 (1CLK), U2.11 (2CLK)
GND: C1.2, C2.2, C3.2, C4.2, C5.2, C6.2, C7.2, C8.2, C9.2, C10.2, C11.2, C12.2, C13.2, J2.3, J2.4, J2.6, J2.8, J3.2 (Ext), R3.2, U1.3 (GND), U2.2 (1D), U2.7 (GND), U2.12 (2D), U3.3 (GND), U4.3 (GND), U5.3 (GND), U6.3 (A), U6.4 (B), U6.5 (C), U6.6 (D), U6.8 (GND), U7.1 (1~OE), U7.4 (2~OE), U7.7 (GND), U7.9 (3A), U7.10 (3~OE), U7.12 (4A), U8.3 (GND), U9.3 (GND), U10.3 (GND), Y1.4 (GND)
unnamed: R6.1, U3.4
unnamed: R7.1, U1.4 (OUT~Y)
unnamed: R8.2, U4.4 (Q)
unnamed: R9.1, U7.3 (1Y)
unnamed: R10.1, U7.6 (2Y)
unnamed: R4.1, U8.4 (OUT~Y)
unnamed: R11.2, U10.4 (OUT~Y)
unnamed: R5.2, Y1.5 (OUT)
