mmosko/Zx50/boards/Zx50_SwitchInterposer/Zx50_SwitchInterposer.kicad_pcb

## KiCad design boards/Zx50_SwitchInterposer/Zx50_SwitchInterposer.kicad_pcb (2026-05-21)

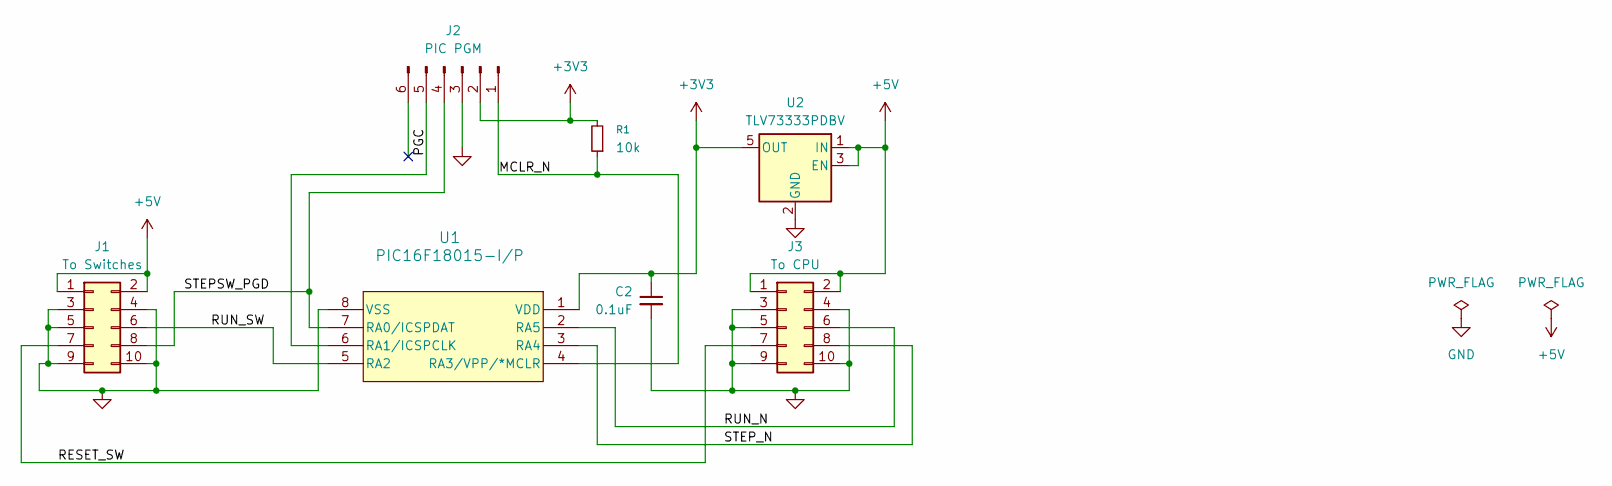
[picture p51: schematic Zx50_SwitchInterposer.kicad_sch]

Parts:
C2: 0.1uF; C_Disc_D5.0mm_W2.5mm_P5.00mm; DigiKey_PN BC1101CT-ND
J1: To Switches; PinSocket_2x05_P2.54mm_Vertical; DigiKey_PN S9194-ND
J2: PIC PGM; PinHeader_1x06_P2.54mm_Horizontal_EDGE; Digi-Key_PN 732-5339-ND
J3: To CPU; IDC-Header_2x05_P2.54mm_Vertical; DigiKey_PN 732-2098-ND
R1: 10k; R_Axial_DIN0207_L6.3mm_D2.5mm_P10.16mm_Horizontal
U1: PIC16F18015-I/P; DIP-8_W7.62mm; DigiKey_PN 150-PIC16F18015-I/P-ND
U2: TLV73333PDBV; SOT-23-5

Connections:
+3V3: C2.1, J2.2, R1.2, U1.1 (VDD), U2.5 (OUT)
+5V: J1.1, J1.2, J3.1, J3.2, U2.1 (IN), U2.3 (EN)
/MCLR_N: J2.1, R1.1, U1.4 (RA3/VPP/*MCLR)
/PGC: J2.5, U1.6 (RA1/ICSPCLK)
/RESET_SW: J1.7, J3.7
/RUN_N: J3.6, U1.2 (RA5)
/RUN_SW: J1.6, U1.5 (RA2)
/STEPSW_PGD: J1.8, J2.4, U1.7 (RA0/ICSPDAT)
/STEP_N: J3.8, U1.3 (RA4)
GND: C2.2, J1.3, J1.4, J1.5, J1.9, J1.10, J2.3, J3.3, J3.4, J3.5, J3.9, J3.10, U1.8 (VSS), U2.2 (GND)

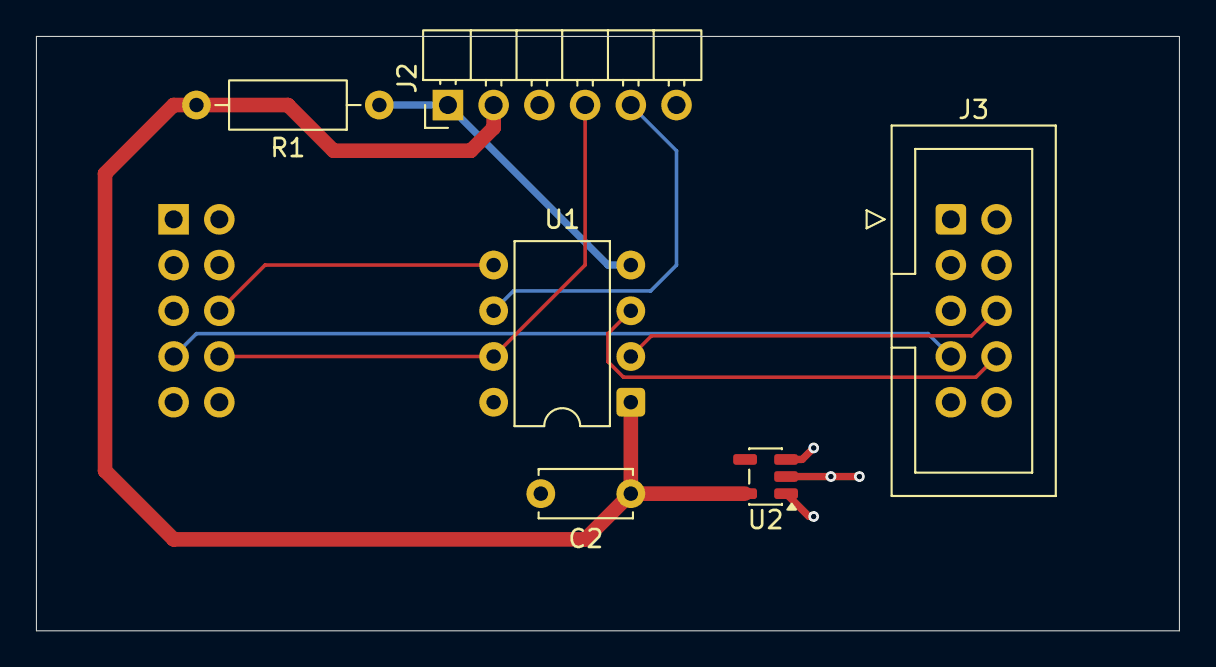
[picture p52: board Zx50_SwitchInterposer.kicad_pcb from above]

Board: 4 copper layers, 63.5 x 33.0 mm, 7 parts (1 on the bottom side), 10 nets.
