mmosko/Zx50/boards/Zx50_FrontPanelCard_RevB/Zx50_FrontPanelCard.kicad_pcb

## KiCad design boards/Zx50_FrontPanelCard_RevB/Zx50_FrontPanelCard.kicad_pcb (2026-05-16, an earlier design)

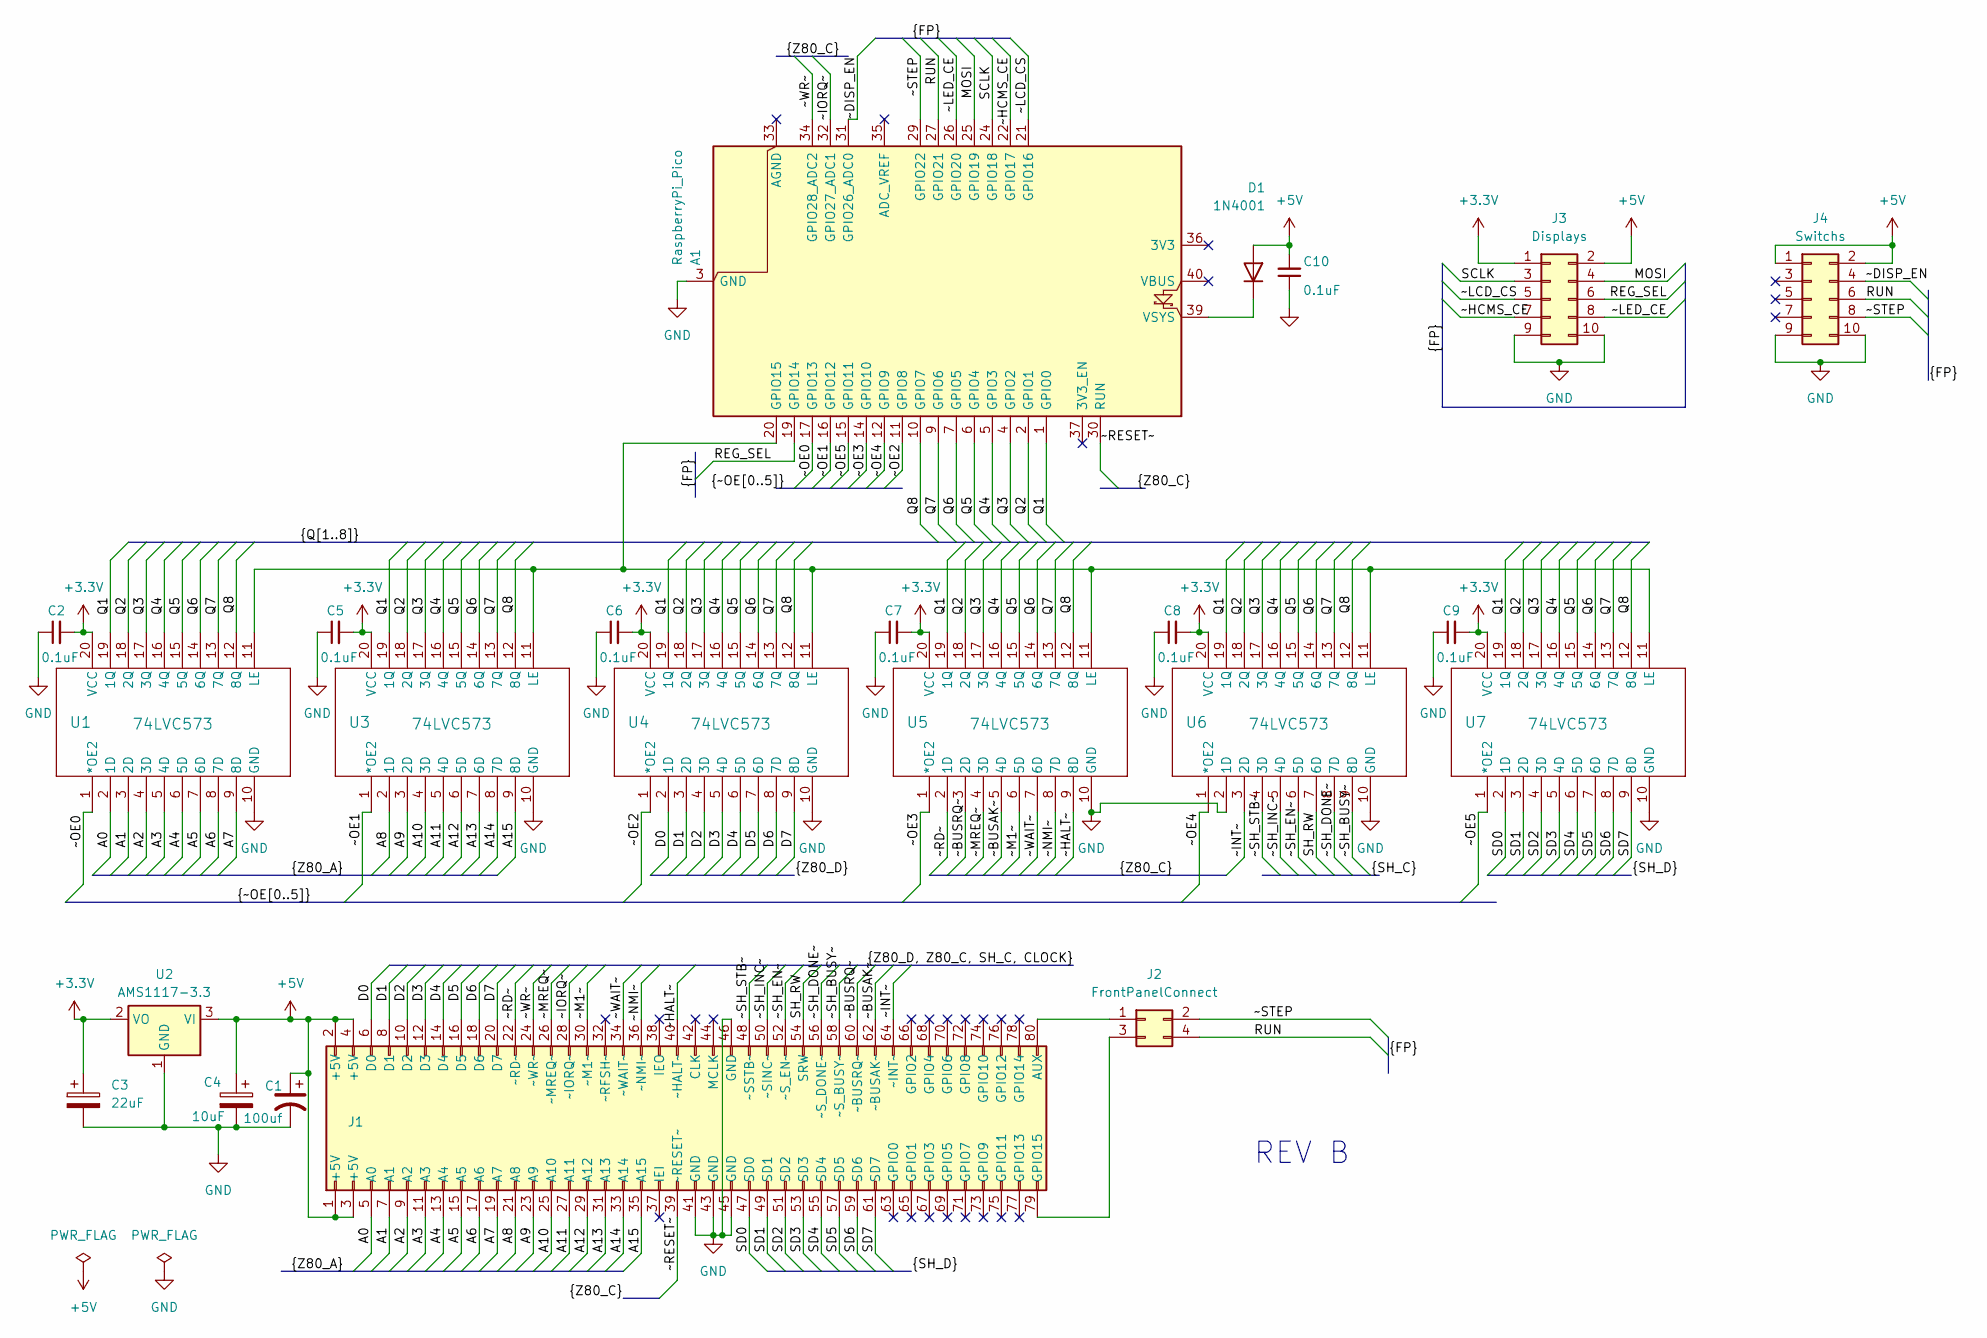
[picture p53: schematic Zx50_FrontPanelCard.kicad_sch]

Parts:
A1: RaspberryPi_Pico; RaspberryPi_Pico_Common_Unspecified; Mouser_PN 358-SC1634; Digi-Key_PN SC1634
C1: 100uf; CP_Radial_D10.0mm_P5.00mm
C2, C5, C6, C7, C8, C9, C10: 0.1uF; C_Disc_D5.0mm_W2.5mm_P5.00mm; DigiKey_PN BC1101CT-ND
C3: 22uF; CP_Radial_Tantal_D5.0mm_P2.50mm; Mouser_PN 80-T350E226K010AT; DigiKey_PN 399-1418-ND
C4: 10uF; CP_Radial_Tantal_D5.0mm_P2.50mm; Mouser_PN 80-T350E106K025; DigiKey_PN 399-1418-ND
D1: 1N4001; D_DO-41_SOD81_P10.16mm_Horizontal
J1: Zx50_EdgeConnector; PinSocket_2x40_P2.54mm_Vertical_Oval; Mouser_PN 737-PH2RA-80-UA; Digi-Key_PN 2057-PH2RA-80-UA-ND
J2: FrontPanelConnect; PinSocket_2x02_P2.54mm_Vertical; DigiKey_PN S1012E-02-ND
J3: Displays; IDC-Header_2x05_P2.54mm_Horizontal_Edge; Mouser_PN 710-61201022921; DigiKey_PN 732-2098-ND
J4: Switchs; IDC-Header_2x05_P2.54mm_Horizontal_Edge; Mouser_PN 710-61201022921; DigiKey_PN 732-2098-ND
U1, U3, U4, U5, U6, U7: 74LVC573; SOIC-20W_7.5x12.8mm_P1.27mm; Mouser_PN 595-SN74LVC573ADW; DigiKey_PN 296-8527-5-ND
U2: AMS1117-3.3; SOT-223-3_TabPin2; Mouser_PN 926-LM1117MPX3.3NOPB

Connections:
+3.3V: C2.2, C3.1, C5.2, C6.2, C7.2, C8.2, C9.2, J3.1, U1.20 (VCC), U2.2 (VO), U3.20 (VCC), U4.20 (VCC), U5.20 (VCC), U6.20 (VCC), U7.20 (VCC)
+5V: C1.1, C4.1, C10.2, D1.2 (A), J1.1 (+5V), J1.2 (+5V), J1.3 (+5V), J1.4 (+5V), J3.2, J4.1, J4.2, U2.3 (VI)
/A0: J1.5 (A0), U1.2 (1D)
/A1: J1.7 (A1), U1.3 (2D)
/A2: J1.9 (A2), U1.4 (3D)
/A3: J1.11 (A3), U1.5 (4D)
/A4: J1.13 (A4), U1.6 (5D)
/A5: J1.15 (A5), U1.7 (6D)
/A6: J1.17 (A6), U1.8 (7D)
/A7: J1.19 (A7), U1.9 (8D)
/A8: J1.21 (A8), U3.2 (1D)
/A9: J1.23 (A9), U3.3 (2D)
/A10: J1.25 (A10), U3.4 (3D)
/A11: J1.27 (A11), U3.5 (4D)
/A12: J1.29 (A12), U3.6 (5D)
/A13: J1.31 (A13), U3.7 (6D)
/A14: J1.33 (A14), U3.8 (7D)
/A15: J1.35 (A15), U3.9 (8D)
/D0: J1.6 (D0), U4.2 (1D)
/D1: J1.8 (D1), U4.3 (2D)
/D2: J1.10 (D2), U4.4 (3D)
/D3: J1.12 (D3), U4.5 (4D)
/D4: J1.14 (D4), U4.6 (5D)
/D5: J1.16 (D5), U4.7 (6D)
/D6: J1.18 (D6), U4.8 (7D)
/D7: J1.20 (D7), U4.9 (8D)
/MOSI: A1.25 (GPIO19), J3.4
/Q1: A1.1 (GPIO0), U1.19 (1Q), U3.19 (1Q), U4.19 (1Q), U5.19 (1Q), U6.19 (1Q), U7.19 (1Q)
/Q2: A1.2 (GPIO1), U1.18 (2Q), U3.18 (2Q), U4.18 (2Q), U5.18 (2Q), U6.18 (2Q), U7.18 (2Q)
/Q3: A1.4 (GPIO2), U1.17 (3Q), U3.17 (3Q), U4.17 (3Q), U5.17 (3Q), U6.17 (3Q), U7.17 (3Q)
/Q4: A1.5 (GPIO3), U1.16 (4Q), U3.16 (4Q), U4.16 (4Q), U5.16 (4Q), U6.16 (4Q), U7.16 (4Q)
/Q5: A1.6 (GPIO4), U1.15 (5Q), U3.15 (5Q), U4.15 (5Q), U5.15 (5Q), U6.15 (5Q), U7.15 (5Q)
/Q6: A1.7 (GPIO5), U1.14 (6Q), U3.14 (6Q), U4.14 (6Q), U5.14 (6Q), U6.14 (6Q), U7.14 (6Q)
/Q7: A1.9 (GPIO6), U1.13 (7Q), U3.13 (7Q), U4.13 (7Q), U5.13 (7Q), U6.13 (7Q), U7.13 (7Q)
/Q8: A1.10 (GPIO7), U1.12 (8Q), U3.12 (8Q), U4.12 (8Q), U5.12 (8Q), U6.12 (8Q), U7.12 (8Q)
/REG_SEL: A1.19 (GPIO14), J3.6
/RUN: A1.27 (GPIO21), J2.4, J4.6
/SCLK: A1.24 (GPIO18), J3.3
/SD0: J1.47 (SD0), U7.2 (1D)
/SD1: J1.49 (SD1), U7.3 (2D)
/SD2: J1.51 (SD2), U7.4 (3D)
/SD3: J1.53 (SD3), U7.5 (4D)
/SD4: J1.55 (SD4), U7.6 (5D)
/SD5: J1.57 (SD5), U7.7 (6D)
/SD6: J1.59 (SD6), U7.8 (7D)
/SD7: J1.61 (SD7), U7.9 (8D)
/SH_RW: J1.54 (SRW), U6.7 (6D)
/~BUSAK~: J1.62 (~BUSAK~), U5.5 (4D)
/~BUSRQ~: J1.60 (~BUSRQ~), U5.3 (2D)
/~DISP_EN: A1.31 (GPIO26_ADC0), J4.4
/~HALT~: J1.40 (~HALT~), U5.9 (8D)
/~HCMS_CE: A1.22 (GPIO17), J3.7
/~INT~: J1.64 (~INT~), U6.3 (2D)
/~IORQ~: A1.32 (GPIO27_ADC1), J1.28 (~IORQ~)
/~LCD_CS: A1.21 (GPIO16), J3.5
/~LED_CE: A1.26 (GPIO20), J3.8
/~M1~: J1.30 (~M1~), U5.6 (5D)
/~MREQ~: J1.26 (~MREQ~), U5.4 (3D)
/~NMI~: J1.36 (~NMI~), U5.8 (7D)
/~OE0: A1.17 (GPIO13), U1.1 (*OE2)
/~OE1: A1.16 (GPIO12), U3.1 (*OE2)
/~OE2: A1.11 (GPIO8), U4.1 (*OE2)
/~OE3: A1.14 (GPIO10), U5.1 (*OE2)
/~OE4: A1.12 (GPIO9), U6.1 (*OE2)
/~OE5: A1.15 (GPIO11), U7.1 (*OE2)
/~RD~: J1.22 (~RD~), U5.2 (1D)
/~RESET~: A1.30 (RUN), J1.39 (~RESET~)
/~SH_BUSY~: J1.58 (~S_BUSY~), U6.9 (8D)
/~SH_DONE~: J1.56 (~S_DONE~), U6.8 (7D)
/~SH_EN~: J1.52 (~S_EN~), U6.6 (5D)
/~SH_INC~: J1.50 (~SINC~), U6.5 (4D)
/~SH_STB~: J1.48 (~SSTB~), U6.4 (3D)
/~STEP: A1.29 (GPIO22), J2.2, J4.8
/~WAIT~: J1.34 (~WAIT~), U5.7 (6D)
/~WR~: A1.34 (GPIO28_ADC2), J1.24 (~WR~)
GND: A1.3 (GND), A1.8 (GND), A1.13 (GND), A1.18 (GND), A1.23 (GND), A1.28 (GND), A1.38 (GND), C1.2, C2.1, C3.2, C4.2, C5.1, C6.1, C7.1, C8.1, C9.1, C10.1, J1.41 (GND), J1.43 (GND), J1.45 (GND), J1.46 (GND), J3.9, J3.10, J4.9, J4.10, U1.10 (GND), U2.1 (GND), U3.10 (GND), U4.10 (GND), U5.10 (GND), U6.2 (1D), U6.10 (GND), U7.10 (GND)
unnamed: A1.20 (GPIO15), U1.11 (LE), U3.11 (LE), U4.11 (LE), U5.11 (LE), U6.11 (LE), U7.11 (LE)
unnamed: A1.39 (VSYS), D1.1 (K)
unnamed: J1.80 (AUX), J2.1
unnamed: J1.79 (GPIO15), J2.3

Notes on the sheet:
REV B

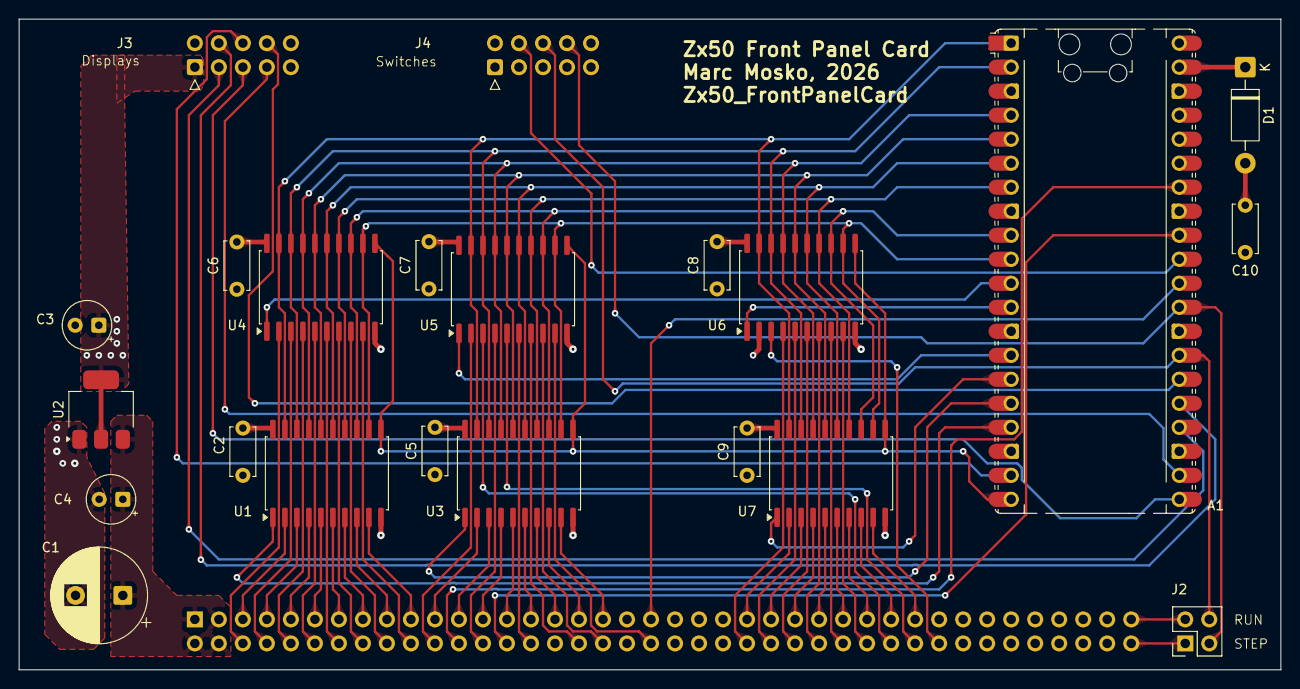
[picture p54: board Zx50_FrontPanelCard.kicad_pcb from above]

Board: 4 copper layers, 133.5 x 68.8 mm, 23 parts (1 on the bottom side), 80 nets.
