mmosko/Zx50/mmu/model_rev1/src/zx50_mem_control.v

`timescale 1ns/1ps

`ifdef HW_REV_A11_BUG
// ==========================================
// ATMEL FITTER PIN CONSTRAINTS (RevA Hardware - A11 Bug)
// TODO: Some of these names were changed need to update
// ==========================================
//PIN: 87 = mclk;
//PIN: 90 = zclk;
//PIN: 89 = reset_n;

//PIN: 40 = duplex_in[3];
//PIN: 37 = duplex_in[2];
//PIN: 35 = duplex_in[1];
//PIN: 33 = duplex_in[0];

//PIN: 41 = z80_m1_n;
//PIN: 42 = z80_iei;
//PIN: 36 = z80_ieo;
//PIN: 96 = z80_int_n;
//PIN: 97 = z80_wait_n;

//PIN: 21 = z80_addr[15];
//PIN: 20 = z80_addr[14];
//PIN: 19 = z80_addr[13];
//PIN: 17 = z80_addr[12];
//PIN: 16 = z80_addr[11];
//PIN: 14 = z80_addr[10];
//PIN: 13 = z80_addr[9];
//PIN: 12 = z80_addr[8];
//PIN: 10 = z80_addr[7];
//PIN: 9  = z80_addr[6];
//PIN: 8  = z80_addr[5];
//PIN: 7  = z80_addr[4];
//PIN: 6  = z80_addr[3];
//PIN: 5  = z80_addr[2];
//PIN: 2  = z80_addr[1];
//PIN: 1  = z80_addr[0];

//PIN: 32 = l_data[7];
//PIN: 31 = l_data[6];
//PIN: 30 = l_data[5];
//PIN: 29 = l_data[4];
//PIN: 28 = l_data[3];
//PIN: 27 = l_data[2];
//PIN: 25 = l_data[1];
//PIN: 24 = l_data[0];

//PIN: 47 = sh_en_n;
//PIN: 48 = sh_rw_n;
//PIN: 46 = sh_inc_n;
//PIN: 45 = sh_stb_n;
//PIN: 49 = sh_done_n;
//PIN: 50 = sh_busy_n;

//PIN: 44 = sh_c_dir;
//PIN: 23 = z80_data_oe_n;
//PIN: 52 = sh_data_oe_n;
//PIN: 22 = l_dir;

//PIN: 85 = l_addr[10];
//PIN: 84 = l_addr[9];
//PIN: 83 = l_addr[8];
//PIN: 81 = l_addr[7];
//PIN: 80 = l_addr[6];
//PIN: 79 = l_addr[5];
//PIN: 78 = l_addr[4];
//PIN: 77 = l_addr[3];
//PIN: 76 = l_addr[2];
//PIN: 75 = l_addr[1];
//PIN: 72 = l_addr[0];

//PIN: 56 = atl_addr[3];
//PIN: 55 = atl_addr[2];
//PIN: 54 = atl_addr[1];
//PIN: 53 = atl_addr[0];

//PIN: 68 = atl_data[7];
//PIN: 67 = atl_data[6];
//PIN: 65 = atl_data[5];
//PIN: 64 = atl_data[4];
//PIN: 63 = atl_data[3];
//PIN: 61 = atl_data[2];
//PIN: 60 = atl_data[1];
//PIN: 58 = atl_data[0];

//PIN: 69 = atl_we_n;
//PIN: 70 = atl_oe_n;
//PIN: 71 = atl_ce_n;

//PIN: 99 = ram_ce0_n;
//PIN: 92 = ram_ce1_n;
//PIN: 98 = rom_ce_n;
//PIN: 93 = mem_oe_n;
//PIN: 94 = ram_we_n;
`else
// ==========================================
// ATMEL FITTER PIN CONSTRAINTS (Clean Hardware)
// ==========================================
`endif

module zx50_mem_control (
    input  wire mclk,
    input  wire zclk,
    input  wire reset_n,

    // Z80 Backplane
    input  wire [15:0] z80_a,
    input  wire b_z80_mreq_n,
    input  wire b_z80_iorq_n,
    input  wire b_z80_rd_n,
    input  wire b_z80_wr_n,
    input  wire b_z80_m1_n,
    
    output wire wait_n, // Driven by Arbiter
    output wire int_n,  // Driven by DMA (Interrupt Pending)

    // Transceiver & Local Bus
    output wire z80_d_oe_n, // Driven by Arbiter/DMA
    output wire d_dir,      // Driven by Arbiter/DMA
    inout  wire [7:0] l_d,
    output wire [10:0] l_a,
    
    output reg  oe_n,
    output reg  we_n,
    output reg  ram_ce0_n,
    output reg  ram_ce1_n,
    output reg  rom_ce2_n,

    // ATL 
    inout  wire [7:0] atl_d,
    output reg  [3:0] atl_a,
    output reg  atl_ce_n,
    output wire  atl_oe_n,
    output reg  atl_we_n,
    
    // Shadow Bus Arbiter Pins
    inout  wire sh_en_n,      // Changed to inout for multidrop
    inout  wire sh_rw_n,      // Changed to inout for multidrop
    inout  wire sh_busy_n,    // Changed to inout for multidrop
    output wire sh_data_oe_n,
    
    // --- NEW: Shadow Bus DMA Pins ---
    inout  wire sh_inc_n,
    inout  wire sh_stb_n,
    inout  wire sh_done_n,
    output wire sh_c_dir
);

    // --- Internal State ---
    reg [1:0]  card_addr; 
    reg        has_boot_rom;
    reg        rom_enabled;
    reg [15:0] page_ownership;
    reg        init_done;

    // Use A[15:12] globally as the logical page index
    wire [3:0] logical_index = z80_a[15:12];

    // --- Hit Detection ---
    // Updated Hit logic for 2-bit ID
    wire is_card_0     = (card_addr == 2'h0);
    // Matches 0x30-0x33 for MMU and 0x40-0x43 for DMA
    wire card_addr_hit = (z80_a[3:2] == 2'b00) && (z80_a[1:0] == card_addr);
    
	wire is_mmu_port = z80_a[7:4] == 4'h3;
   wire is_dma_port = z80_a[7:4] == 4'h4;
	 
    wire iorq_wr_hit = (!b_z80_iorq_n && !b_z80_wr_n);
    wire mmu_snoop_wr  = (iorq_wr_hit && is_mmu_port);
    wire mmu_direct_wr = mmu_snoop_wr && card_addr_hit;
    
    // DMA IO Decoding (Port 0x4X)
    wire dma_io_write  = (iorq_wr_hit && is_dma_port && card_addr_hit);

    // ROM is active if it's Card 0, ROM is enabled, accessing the lower 32K, during a memory cycle
    (* keep = 1 *) wire effective_use_rom = is_card_0 && rom_enabled && (z80_a[15] == 1'b0) && !b_z80_mreq_n;

    // RAM is active if it's a memory cycle, we own the logical page (A15-A12), and the ROM isn't overriding it
    wire ram_hit = !b_z80_mreq_n && page_ownership[logical_index] && !effective_use_rom;

    // --- DMA Wires & INTACK ---
    wire dma_is_active, dma_is_master, dma_dir_to_bus, dma_int_pending;
    wire [19:0] dma_phys_addr;
    wire dma_local_we_n, dma_local_oe_n;

    wire intack_cycle = !b_z80_m1_n && !b_z80_iorq_n;
    // Split the intack flag into two separate macrocells to bypass routing congestion!
	 wire intack_value = intack_cycle && dma_int_pending;
    wire respond_intack_lo = intack_value;
    wire respond_intack_hi = intack_value;
    
    // --- Global Z80 Card Hit ---
    wire z80_card_hit = ram_hit || effective_use_rom || mmu_direct_wr || dma_io_write || respond_intack_lo;
    
    // --- Bus Arbiter Instantiation ---
    wire arbiter_z80_data_oe_n, arbiter_l_dir;
    
    zx50_bus_arbiter arbiter (
        .mclk(mclk), 
        .reset_n(reset_n),
        .sh_en_n(sh_en_n), 
        .z80_card_hit(z80_card_hit),
        .z80_wait_n(wait_n), 
        .sh_busy_n(sh_busy_n),
        .z80_rd_n(b_z80_rd_n), 
        .sh_rw_n(sh_rw_n),
        .z80_data_oe_n(arbiter_z80_data_oe_n), 
        .sh_data_oe_n(sh_data_oe_n),
        .l_dir(arbiter_l_dir)
    );

    // 1-stage edge detector for INTACK clear
    reg iorq_sync;
    always @(posedge zclk or negedge reset_n) begin // FIX: Use zclk for Z80 synchronization
        if (!reset_n) iorq_sync <= 1'b1;
        else iorq_sync <= b_z80_iorq_n;
    end
    wire iorq_rising = (!iorq_sync && b_z80_iorq_n);
    wire intack_clear = iorq_rising && dma_int_pending;

    zx50_dma dma (
        .mclk(mclk), .reset_n(reset_n),
        .z80_addr_hi(z80_a[15:8]), .z80_data_in(l_d),
        .z80_iorq_n(b_z80_iorq_n), .dma_io_write(dma_io_write),
        .dma_phys_addr(dma_phys_addr),
        .dma_local_we_n(dma_local_we_n), .dma_local_oe_n(dma_local_oe_n),
        .sh_en_n(sh_en_n), .sh_rw_n(sh_rw_n), .sh_inc_n(sh_inc_n),
        .sh_stb_n(sh_stb_n), .sh_done_n(sh_done_n), .sh_busy_n(sh_busy_n),
        .dma_active(dma_is_active), .sh_c_dir(sh_c_dir), .dma_dir_to_bus(dma_dir_to_bus),
        .dma_is_master(dma_is_master), .int_pending(dma_int_pending), .intack_clear(intack_clear)
    );

    assign int_n = dma_int_pending ? 1'b0 : 1'bz;

    // --- Dynamic Routing (Cycle Stealing) ---
    // If DMA is active, force Z80 transceiver closed. Otherwise let Arbiter decide.
    assign z80_d_oe_n = dma_is_active ? 1'b1 : arbiter_z80_data_oe_n;
    
    // Force direction outward (Card -> Z80) during INTACK, since RD_n is high.
    assign d_dir = (dma_is_active && dma_dir_to_bus) ? 1'b0 : 
                   (respond_intack_hi) ? 1'b0 : 
                   arbiter_l_dir;

    assign l_a = dma_is_active ? dma_phys_addr[10:0] : z80_a[10:0];
    wire active_a11 = dma_is_active ? dma_phys_addr[11] : z80_a[11];

    // Drive ATL Data Bus (Or route DMA Address High bits)
	 wire use_rom_no_dma = effective_use_rom && !dma_is_active;
	 
    wire cpld_driving_atl = mmu_direct_wr || use_rom_no_dma || dma_is_active;
	 wire local_atl_oe_n = !(ram_hit && !cpld_driving_atl);
	 
    // If the CPLD owns the bus, this is the value it output to atl_d
 	  wire [7:0] local_atl_d = (mmu_direct_wr ? l_d : 
                   (use_rom_no_dma ? {3'b000, z80_a[15:11]} : 
                   dma_phys_addr[19:12]));
						 
	 // If the CPLD is not driving atl_d, should it tristate or park it?
	  wire [7:0] idle_atl_d = (local_atl_oe_n ? 8'h00 : 8'hZZ);
	 
    assign atl_d = cpld_driving_atl ? local_atl_d : idle_atl_d;

    // The external ATL SRAM is ONLY allowed to output data when the CPLD is NOT driving the bus.
    // AND we must be doing a standard RAM read (ram_hit)
    assign atl_oe_n = local_atl_oe_n;
    
    // SAFETY INTERLOCK: 
    // True only if Z80 Buffer is OFF, Shadow Buffer is OFF, and Memory is OFF
    wire l_d_idle = (z80_d_oe_n && sh_data_oe_n && oe_n);

	 
	     // Updated Vector: Uses bitwise OR to set the 0x40 base correctly
    wire [7:0] interrupt_vector = 8'h40 | {6'b0, card_addr};
	 
    // SPLIT ASSIGNMENT: Lower nibble driven by _lo flag, upper by _hi flag
    //assign l_d[3:0] = respond_intack_lo ? interrupt_vector[3:0] : (l_d_idle ? 4'h0 : 4'hZ);
    //assign l_d[7:4] = respond_intack_hi ? interrupt_vector[7:4] : (l_d_idle ? 4'h0 : 4'hZ);

	 assign l_d = intack_value ? interrupt_vector : (l_d_idle ? 8'h0 : 8'hZ);
	 
    // --- Combinatorial Pin Routing ---
    always @(*) begin
        // 1. Safe Defaults (Idle State)
        oe_n       = 1'b1;
        we_n       = 1'b1;
        ram_ce0_n  = 1'b1;
        ram_ce1_n  = 1'b1;
        rom_ce2_n  = 1'b1;
        atl_ce_n   = 1'b1;
        // atl_oe_n is driven separately
        // atl_oe_n   = 1'b1;
        atl_we_n   = 1'b1;
        // atl_a      = 4'h0;
        atl_a      = logical_index; // Hard-wired to [15:12] for all modes!

        if (dma_is_active) begin
            // ----------------------------------------------------------------
            // DMA CYCLE STEALING OVERRIDE
            // ----------------------------------------------------------------
            atl_a = 4'h0; // DMA still forces base page
            atl_ce_n = 1'b1; // Bypass ATL, DMA provides full physical address
            // atl_oe_n = 1'b1;
            
            // Physical DMA should ALWAYS be able to hit the Boot ROM, regardless
            // of whether the Z80 has logically unmapped it (rom_enabled)!
            if (is_card_0 && has_boot_rom && dma_phys_addr[19:15] == 5'h00) begin
                rom_ce2_n = 1'b0;
                oe_n = dma_local_oe_n;
                we_n = 1'b1; // ROM is strictly read-only
            end else begin
                // Toggle RAM chips based on DMA's physical address
                if (active_a11 == 1'b0) ram_ce0_n = 1'b0;
                else                    ram_ce1_n = 1'b0;
                
                oe_n = dma_local_oe_n;
                we_n = dma_local_we_n;
            end

        end else if (mmu_direct_wr) begin
            // ----------------------------------------------------------------
            // MMU WRITE ROUTING
            // ----------------------------------------------------------------
            atl_ce_n   = 1'b0;
            atl_we_n   = b_z80_wr_n;
            
        end else if (effective_use_rom) begin
            // ----------------------------------------------------------------
            // ROM READ ROUTING (ATL Bypass)
            // ----------------------------------------------------------------
            atl_ce_n  = 1'b1;
            atl_we_n  = 1'b1;
            
            rom_ce2_n = 1'b0;
            oe_n      = b_z80_rd_n;
            we_n      = 1'b1; 
            
        end else if (ram_hit) begin
            // ----------------------------------------------------------------
            // NORMAL RAM ROUTING (Via ATL)
            // ----------------------------------------------------------------
            atl_ce_n  = 1'b0;
            // Output Enable the ATL SRAM to get the phys page
            atl_we_n  = 1'b1;
            
            // Toggle RAM chips based directly on the A11 bit
            if (z80_a[11] == 1'b0) ram_ce0_n = 1'b0;
            else                   ram_ce1_n = 1'b0;
            
            oe_n = b_z80_rd_n;
            we_n = b_z80_wr_n;
        end
    end

    // --- Synchronous Logic ---
    always @(posedge zclk) begin
if (!reset_n) begin
            // Sample only 2 bits for card ID (using RD and WR as strap pins)
            card_addr      <= {b_z80_rd_n, b_z80_wr_n};
            
            // FIX: Sample pins directly to avoid reset race condition
            has_boot_rom   <= ({b_z80_rd_n, b_z80_wr_n} == 2'h0);
            rom_enabled    <= ({b_z80_rd_n, b_z80_wr_n} == 2'h0);
            
            page_ownership <= 16'h0000;
            init_done      <= 1'b0;

        end else begin
            if (!init_done) begin
                // Execute exactly once after reset goes high
                init_done <= 1'b1;
                // page_ownership[15:8] <= 8'h00; // Claim upper 32K by default (Unmapped, but safe for RAM)
                if (has_boot_rom) page_ownership[7:0] <= 8'hFF; // Auto-claim lower 32K if we have a boot ROM, otherwise claim nothing
                // if (has_boot_rom) page_ownership <= 16'h00FF : 16'h0000; // Auto-claim lower 32K
            end

            // Distributed MMU Snooping
            if (mmu_snoop_wr) begin
                
                // ROM KILL-SWITCH FIX: If ANY card maps a page into the lower 32K 
                // Disable ROM only if we are mapping into the 0x0000-0x7FFF range (Indices 0-7)
                if (logical_index[3] == 1'b0) rom_enabled <= 1'b0;

					 page_ownership[logical_index] <= mmu_direct_wr;
					  
                //if (mmu_direct_wr) begin
                //    // Claim the page
                //    page_ownership[logical_index] <= 1'b1;
                //end else begin
                //    // Another card claimed it! Drop ownership.
                //    page_ownership[logical_index] <= 1'b0;
                //end
            end
            
        end
    end

endmodule
