mmosko/Zx50/mmu/model_rev1/src/zx50_dma.v

`timescale 1ns/1ps

/***************************************************************************************
 * MODULE: zx50_dma (12-Bit Adder & High Fitter Optimization)
 * =====================================================================================
 * DESCRIPTION:
 * Universal Shadow Bus Node. Acts as a highly specialized Block DMA controller 
 * that negotiates transfers across a shared physical backplane.
 *
 * CPLD FITTING OPTIMIZATION 1 (THE 4K PAGE LIMIT):
 * To fit within the tight routing constraints of a 128-macrocell CPLD, the 20-bit 
 * address counter has been split. It uses a static 8-bit upper address latch (A19-A12) 
 * and a fast 12-bit lower address counter (A11-A0).
 * SOFTWARE RULE: DMA transfers will smoothly increment up to 4,096 bytes, but will 
 * wrap around physical 4KB boundaries (A12). The Z80 programmer must manually chunk 
 * transfers that cross logical page boundaries.
 *
 * CPLD FITTING OPTIMIZATION 2 (CENTRALIZED DECODING):
 * Address bus decoding logic is centralized in the top-level core to reduce macrocell 
 * Fan-In. This module only receives the upper address byte and a single, pre-decoded 
 * boolean `dma_io_write` flag.
 *
 * CPLD FITTING OPTIMIZATION 3 (DEAD DATA ELIMINATION):
 * The DMA module is strictly an Address Generator and Strobe Sequencer. The 
 * actual 8-bit data payload flows externally between the local bus and the 
 * Shadow Bus transceivers. Dead internal pass-through routing has been purged.
 ***************************************************************************************/

module zx50_dma (
    input  wire mclk,
    input  wire reset_n,

    // --- Z80 Configuration Interface (Highly Optimized) ---
    // Only the upper byte of the address bus is passed to unpack the DMA operand.
    input  wire [7:0] z80_addr_hi, 
    input  wire [7:0] z80_data_in,
    
    // Used to detect the end of the OUT cycle to safely arm the state machine
    input  wire z80_iorq_n,        
    
    // Centralized boolean hit flag from the top-level routing matrix
    input  wire dma_io_write,      

    // --- DMA Local Bus Master Output ---
    output wire [19:0] dma_phys_addr, 
    output wire dma_local_we_n,       
    output wire dma_local_oe_n,       

    // --- Shadow Bus Controls ---
    inout  wire sh_en_n,
    inout  wire sh_rw_n,
    inout  wire sh_inc_n,
    inout  wire sh_stb_n,
    inout  wire sh_done_n,
    input  wire sh_busy_n,

    // --- Internal Status & Interrupts ---
    output wire dma_active, 
    output wire sh_c_dir,
    output wire dma_dir_to_bus,
    output wire dma_is_master, 
    
    output reg  int_pending,
    input  wire intack_clear
);

    // ==========================================
    // 1. DYNAMIC PORT DECODING & BIT-UNPACKING
    // ==========================================
    // Extract the opcode (A15) and 15-bit operand (A14-A8 + D7-D0)
    wire opcode         = z80_addr_hi[7];
    wire [14:0] operand = {z80_addr_hi[6:0], z80_data_in[7:0]};

    // --- OPTIMIZED REGISTERS ---
    reg [7:0]  phys_addr_hi;   // Static upper latch (A19-A12)
    reg [11:0] phys_addr_lo;   // Fast lower counter (A11-A0)
    
    reg [7:0]  byte_count;
    reg is_master;
    reg dir_from_bus;
    reg transfer_armed;
    reg arm_req;

    assign dma_dir_to_bus = !dir_from_bus;
    assign dma_is_master  = is_master;

    // ==========================================
    // 2. STATE MACHINE DECLARATIONS
    // ==========================================
    wire dma_go = transfer_armed;

    localparam M_IDLE   = 3'd0;
    localparam M_START  = 3'd1;
    localparam M_STROBE = 3'd2;
    localparam M_INC    = 3'd3;
    localparam M_WAIT   = 3'd4;
    localparam M_DONE   = 3'd5;

    reg [2:0] m_state;

    wire local_inc  = is_master ? (m_state == M_INC)  : (!is_master && dma_go && !sh_inc_n);
    wire local_done = is_master ? (m_state == M_DONE) : (!is_master && dma_go && !sh_done_n);

    // ==========================================
    // 3. CONFIGURATION REGISTER LATCHING
    // ==========================================
    always @(posedge mclk or negedge reset_n) begin
        if (!reset_n) begin
            phys_addr_hi   <= 8'h00;
            phys_addr_lo   <= 12'h000;
            byte_count     <= 8'h00;
            is_master      <= 1'b0;
            dir_from_bus   <= 1'b0;
            transfer_armed <= 1'b0;
            arm_req        <= 1'b0;
        end else if (dma_io_write) begin
            if (opcode == 1'b0) begin
                // OPCODE 0: Setup
                is_master         <= operand[14];
                dir_from_bus      <= operand[13];
                phys_addr_lo      <= operand[11:0];     // Load 4K offset (A11-A0)
                phys_addr_hi[0]   <= operand[12];       // Load A12
            end else begin
                // OPCODE 1: Arm & High Address
                byte_count        <= operand[14:7];
                phys_addr_hi[7:1] <= operand[6:0];      // Load A19-A13
                arm_req           <= 1'b1;
            end
        // Safely wait for the Z80 to finish its OUT instruction before blasting the bus
        end else if (arm_req && z80_iorq_n) begin
            transfer_armed <= 1'b1;
            arm_req        <= 1'b0;
            
        end else if (local_inc) begin
		  
		      // Let the CPLD's native hardware carry-chain (Parallel Expanders) handle the math!
            phys_addr_lo <= phys_addr_lo + 1'b1;
            byte_count   <= byte_count - 1'b1;
				
				/*
            // ----------------------------------------------------------------
            // CPLD FITTER OPTIMIZATION: MANUAL COUNTER SPLITTING
            // By manually breaking the counters into 4-bit and 6-bit chunks, we 
            // prevent Quartus from inferring rigid LPM carry-chains that cannot 
            // reach the locked physical I/O pins on the package edges.
            // ----------------------------------------------------------------
            
            // Increment lower 6 bits (A5-A0)
            phys_addr_lo[5:0] <= phys_addr_lo[5:0] + 1'b1;
            
            // Carry into upper 6 bits (A11-A6) only when lower rolls over
            if (phys_addr_lo[5:0] == 6'h3F) begin
                phys_addr_lo[11:6] <= phys_addr_lo[11:6] + 1'b1;
            end

            // Decrement lower 4 bits
            byte_count[3:0] <= byte_count[3:0] - 1'b1;
            
            // Borrow from upper 4 bits only when lower underflows
            if (byte_count[3:0] == 4'h0) begin
                byte_count[7:4] <= byte_count[7:4] - 1'b1;
            end
            */
				
        end else if (local_done) begin
            transfer_armed <= 1'b0;
        end
    end

    // ==========================================
    // 4. CYCLE STEALING: HIERARCHICAL YIELD LOGIC
    // ==========================================
    wire yield_req = (sh_busy_n == 1'b0);

    (* keep = 1 *) wire safe_to_yield = is_master ?
        (m_state == M_IDLE || m_state == M_START || m_state == M_WAIT || m_state == M_DONE) 
        : (sh_en_n !== 1'b0);

    reg yielding;
    
    always @(posedge mclk or negedge reset_n) begin
        if (!reset_n) yielding <= 1'b0;
        else if (yield_req && safe_to_yield) yielding <= 1'b1;
        else if (!yield_req) yielding <= 1'b0;
    end

    assign dma_active = dma_go && !yielding;

    // ==========================================
    // 5. MASTER STATE MACHINE
    // ==========================================
    always @(posedge mclk or negedge reset_n) begin
        if (!reset_n) begin
            m_state <= M_IDLE;
            int_pending <= 1'b0;
        end else begin
            if (intack_clear) int_pending <= 1'b0;
            
            if (is_master) begin
                case (m_state)
                    M_IDLE:   if (dma_go && !yielding && !yield_req) m_state <= M_START;
                    M_START:  if (!yielding && !yield_req) m_state <= M_STROBE;
                    M_STROBE: m_state <= (byte_count == 8'h00) ? M_DONE : M_INC;
                    M_INC:    m_state <= M_WAIT;
                    M_WAIT:   if (!yielding && !yield_req) m_state <= M_STROBE;
                    M_DONE:   begin
                        int_pending <= 1'b1;
                        m_state <= M_IDLE;
                    end
                    default:  m_state <= M_IDLE;
                endcase
            end
        end
    end

    // ==========================================
    // 6. PHYSICAL TRANSCEIVER AND BUS ROUTING
    // ==========================================
    assign sh_c_dir  = !dir_from_bus;
    
    wire generated_stb_n = !(m_state == M_STROBE);
    // wire int_sh_stb_n    = is_master ? generated_stb_n : sh_stb_n;
    
    assign sh_en_n   = (is_master && dma_go && m_state != M_IDLE) ? 1'b0 : 1'bz;
    assign sh_rw_n   = (is_master && dma_go && m_state != M_IDLE) ? dir_from_bus : 1'bz;
    assign sh_stb_n  = (is_master && dma_go && m_state != M_IDLE) ? generated_stb_n : 1'bz;
    assign sh_inc_n  = (is_master && dma_go && m_state == M_INC) ? 1'b0 : 1'bz;
    assign sh_done_n = (is_master && dma_go && m_state == M_DONE) ? 1'b0 : 1'bz;
    
    // Concatenate the static high bits and the fast 4K counter for the local address
    assign dma_phys_addr = {phys_addr_hi, phys_addr_lo};
    
    // ==========================================
    // LOCAL MEMORY CONTROL
    // ==========================================
    wire active_transfer = (is_master && dma_go && m_state != M_IDLE) || (!is_master && dma_go);
    
    // OE stays continuously LOW for the entire transfer to guarantee massive Data Hold Time!
    assign dma_local_oe_n = (active_transfer && !dir_from_bus) ? 1'b0 : 1'b1;
    
    // WE pulses LOW exactly with the strobe
    assign dma_local_we_n = (active_transfer && dir_from_bus) ? 
                            (is_master ? generated_stb_n : sh_stb_n) : 1'b1;
endmodule
