mmosko/Zx50/mmu/model/src/zx50_cpld_core.v

`timescale 1ns/1ps

/***************************************************************************************
 * MODULE: zx50_cpld_core (Rev A - Fit Optimizations)
 ***************************************************************************************/

`ifdef HW_REV_A11_BUG
// ==========================================
// ATMEL FITTER PIN CONSTRAINTS (RevA Hardware - A11 Bug)
// ==========================================
//PIN: 87 = mclk;
//PIN: 89 = reset_n;

//PIN: 40 = duplex_in[3];
//PIN: 37 = duplex_in[2];
//PIN: 35 = duplex_in[1];
//PIN: 33 = duplex_in[0];

//PIN: 41 = z80_m1_n;
//PIN: 42 = z80_iei;
//PIN: 36 = z80_ieo;
//PIN: 96 = z80_int_n;
//PIN: 97 = z80_wait_n;

//PIN: 21 = z80_addr[15];
//PIN: 20 = z80_addr[14];
//PIN: 19 = z80_addr[13];
//PIN: 17 = z80_addr[12];
//PIN: 16 = z80_addr[11];
//PIN: 14 = z80_addr[10];
//PIN: 13 = z80_addr[9];
//PIN: 12 = z80_addr[8];
//PIN: 10 = z80_addr[7];
//PIN: 9  = z80_addr[6];
//PIN: 8  = z80_addr[5];
//PIN: 7  = z80_addr[4];
//PIN: 6  = z80_addr[3];
//PIN: 5  = z80_addr[2];
//PIN: 2  = z80_addr[1];
//PIN: 1  = z80_addr[0];

//PIN: 32 = l_data[7];
//PIN: 31 = l_data[6];
//PIN: 30 = l_data[5];
//PIN: 29 = l_data[4];
//PIN: 28 = l_data[3];
//PIN: 27 = l_data[2];
//PIN: 25 = l_data[1];
//PIN: 24 = l_data[0];

//PIN: 47 = sh_en_n;
//PIN: 48 = sh_rw_n;
//PIN: 46 = sh_inc_n;
//PIN: 45 = sh_stb_n;
//PIN: 49 = sh_done_n;
//PIN: 50 = sh_busy_n;

//PIN: 44 = sh_c_dir;
//PIN: 23 = z80_data_oe_n;
//PIN: 52 = sh_data_oe_n;
//PIN: 22 = l_dir;

//PIN: 85 = l_addr[10];
//PIN: 84 = l_addr[9];
//PIN: 83 = l_addr[8];
//PIN: 81 = l_addr[7];
//PIN: 80 = l_addr[6];
//PIN: 79 = l_addr[5];
//PIN: 78 = l_addr[4];
//PIN: 77 = l_addr[3];
//PIN: 76 = l_addr[2];
//PIN: 75 = l_addr[1];
//PIN: 72 = l_addr[0];

//PIN: 56 = atl_addr[3];
//PIN: 55 = atl_addr[2];
//PIN: 54 = atl_addr[1];
//PIN: 53 = atl_addr[0];

//PIN: 68 = atl_data[7];
//PIN: 67 = atl_data[6];
//PIN: 65 = atl_data[5];
//PIN: 64 = atl_data[4];
//PIN: 63 = atl_data[3];
//PIN: 61 = atl_data[2];
//PIN: 60 = atl_data[1];
//PIN: 58 = atl_data[0];

//PIN: 69 = atl_we_n;
//PIN: 70 = atl_oe_n;
//PIN: 71 = atl_ce_n;

//PIN: 99 = ram_ce0_n;
//PIN: 92 = ram_ce1_n;
//PIN: 98 = rom_ce_n;
//PIN: 93 = mem_oe_n;
//PIN: 94 = ram_we_n;
`else
// ==========================================
// ATMEL FITTER PIN CONSTRAINTS (Clean Hardware)
// ==========================================
`endif

module zx50_cpld_core (
    input  wire mclk,
    input  wire reset_n,
    
    input  wire [3:0] duplex_in, 
    input  wire z80_m1_n,       
    input  wire z80_iei,        
    output wire z80_ieo,        
    inout wire z80_int_n,    
    inout wire z80_wait_n,   
    input  wire [15:0] z80_addr, 

    inout  wire [7:0] l_data, 
    
    inout  wire sh_en_n, 
    inout  wire sh_rw_n, 
    inout  wire sh_inc_n, 
    inout  wire sh_stb_n, 
    inout  wire sh_done_n, 
    inout  wire sh_busy_n, 
    
    output wire sh_c_dir,         
    output wire z80_data_oe_n, 
    output wire sh_data_oe_n,
    output wire l_dir,
 
    output wire [11:0] l_addr,  
    output wire [3:0]  atl_addr, 
    inout  wire [7:0]  atl_data, 
    
    output wire atl_we_n, 
    output wire atl_oe_n, 
    output wire atl_ce_n,
    output wire ram_ce0_n, 
    output wire ram_ce1_n,
    output wire rom_ce_n,      
    output wire ram_oe_n,
    output wire ram_we_n        
);

    // ==========================================
    // 1. DUPLEX CONFIGURATION LATCH
    // ==========================================
    reg [3:0] latched_id;
    wire z80_rd_n   = duplex_in[0]; 
    wire z80_wr_n   = duplex_in[1]; 
    wire z80_mreq_n = duplex_in[2]; 
    wire z80_iorq_n = duplex_in[3];

    always @(posedge mclk) begin
        if (!reset_n) latched_id <= duplex_in;
    end

    wire mmu_boot_en_n = (!reset_n) ? (duplex_in != 4'h0) : (latched_id != 4'h0);

    // ==========================================
    // 2. INTERNAL SUBSYSTEM WIRES & HIT LOGIC
    // ==========================================
    wire internal_active, mmu_busy;
    wire mmu_cpu_updating;
    
    wire dma_is_active, dma_int_pending, dma_is_master;
    wire safe_z80_iorq_n = dma_is_active ? 1'b1 : z80_iorq_n;

    wire mmu_snoop_wr  = (!safe_z80_iorq_n && !z80_wr_n && ((z80_addr[7:0] & 8'hF0) == 8'h30));
    wire mmu_direct_wr = mmu_snoop_wr && (z80_addr[7:0] == (8'h30 | latched_id));
    wire dma_io_write  = (!z80_iorq_n && !z80_wr_n && (z80_addr[7:0] == (8'h40 | latched_id)));

    wire active_bus_cycle = !z80_mreq_n || !z80_iorq_n;
    wire mmu_card_hit;
    wire qualified_mmu_hit = mmu_card_hit && active_bus_cycle;
    wire dma_card_hit = (!z80_iorq_n && (z80_addr[7:0] == (8'h40 | latched_id))); 
    wire internal_z80_card_hit = qualified_mmu_hit | dma_card_hit;

    wire arbiter_sh_busy_n, arbiter_l_dir, arbiter_z80_data_oe_n;
    wire arbiter_sh_data_oe_n, arbiter_wait_n;
    
    wire [19:0] dma_phys_addr;
    wire dma_local_we_n, dma_local_oe_n, dma_dir_to_bus;

    wire memory_cycle = !z80_mreq_n;
    wire internal_z80_data_oe_n = dma_is_active ? 1'b1 : arbiter_z80_data_oe_n;
    wire internal_l_dir         = arbiter_l_dir; 
    wire z80_grant = !internal_z80_data_oe_n;

    // ==========================================
    // 3. INTERRUPT & INTACK LOGIC
    // ==========================================
    wire intack_cycle = !z80_m1_n && !z80_iorq_n;
    wire responding_to_intack = intack_cycle && z80_iei && dma_int_pending;

    // OPTIMIZATION: 1-stage edge detector.
    reg iorq_sync;
    always @(posedge mclk or negedge reset_n) begin
        if (!reset_n) iorq_sync <= 1'b1;
        else iorq_sync <= z80_iorq_n;
    end
    
    wire iorq_rising = (!iorq_sync && z80_iorq_n);
    wire intack_clear = iorq_rising && z80_iei && dma_int_pending;

    assign z80_int_n = dma_int_pending ? 1'b0 : 1'bz;
    assign z80_ieo = z80_iei && !dma_int_pending; 

    // ==========================================
    // 4. CORE SUB-MODULE INSTANTIATIONS
    // ==========================================
    wire arbiter_hit  = internal_z80_card_hit || responding_to_intack;
    wire arbiter_rd_n = responding_to_intack ? 1'b0 : z80_rd_n;

    zx50_bus_arbiter arbiter_unit (
        .mclk(mclk), .reset_n(reset_n),
        .sh_en_n(sh_en_n), 
        .z80_card_hit(arbiter_hit), 
        .z80_wait_n(arbiter_wait_n), .sh_busy_n(arbiter_sh_busy_n), 
        .z80_rd_n(arbiter_rd_n), .sh_rw_n(sh_rw_n),
        .z80_data_oe_n(arbiter_z80_data_oe_n), 
        .sh_data_oe_n(arbiter_sh_data_oe_n), 
        .l_dir(arbiter_l_dir)                  
    );

    wire mmu_atl_oe_n;
    wire mmu_is_rom_enabled;

    zx50_mmu_sram mmu_unit (
        .mclk(mclk), .reset_n(reset_n), 
        .boot_en_n(mmu_boot_en_n), 
        .z80_addr_hi(z80_addr[15:8]),   
        .mmu_snoop_wr(mmu_snoop_wr),    
        .mmu_direct_wr(mmu_direct_wr),  
        .z80_mreq_n(z80_mreq_n), 
        .atl_addr(atl_addr), .atl_we_n(atl_we_n), .atl_oe_n(mmu_atl_oe_n), 
        .active(internal_active),
        .cpu_updating(mmu_cpu_updating),
        .z80_card_hit(mmu_card_hit), 
        .is_busy(mmu_busy),
        .is_rom_enabled(mmu_is_rom_enabled)
    );

    wire dma_internal_sh_c_dir; 
    wire combined_sh_busy_n = sh_busy_n & arbiter_sh_busy_n;

    zx50_dma dma_unit (
        .mclk(mclk), .reset_n(reset_n), 
        .z80_addr_hi(z80_addr[15:8]),   
        .z80_data_in(l_data), 
        .z80_iorq_n(z80_iorq_n), 
        .dma_io_write(dma_io_write),    
        .dma_phys_addr(dma_phys_addr), 
        .dma_local_we_n(dma_local_we_n), .dma_local_oe_n(dma_local_oe_n),
        .sh_en_n(sh_en_n), .sh_rw_n(sh_rw_n), .sh_inc_n(sh_inc_n),
        .sh_stb_n(sh_stb_n), .sh_done_n(sh_done_n), 
        .sh_busy_n(combined_sh_busy_n), 
        .dma_active(dma_is_active), .sh_c_dir(dma_internal_sh_c_dir), .dma_dir_to_bus(dma_dir_to_bus),
        .dma_is_master(dma_is_master), .int_pending(dma_int_pending), .intack_clear(intack_clear)
    );

    // ==========================================
    // 5. LOCAL MEMORY & LUT MULTIPLEXING
    // ==========================================
    assign atl_ce_n = dma_is_active ? 1'b1 : !(internal_z80_card_hit || mmu_busy);

    wire dma_hitting_rom = (dma_phys_addr[19:15] == 5'b00000);
    wire z80_hitting_rom = (z80_addr[15] == 1'b0) && memory_cycle;
    wire target_is_rom_space = dma_is_active ? dma_hitting_rom : z80_hitting_rom;
    wire effective_use_rom = (latched_id == 4'h0) && mmu_is_rom_enabled && target_is_rom_space; 

    assign atl_oe_n = (dma_is_active || effective_use_rom) ? 1'b1 : mmu_atl_oe_n;

    // --- TRI-STATE LOGIC (ATL DATA BUS) ---
    wire atl_drive_en = dma_is_active | mmu_cpu_updating | effective_use_rom;

    `ifdef HW_REV_A11_BUG
        assign l_addr[10:0] = dma_is_active ? dma_phys_addr[10:0] : z80_addr[10:0];
        assign l_addr[11]   = 1'b0;
        
        wire active_a11 = dma_is_active ? dma_phys_addr[11] : z80_addr[11];
        
        wire safe_to_access_ram = dma_is_active || (internal_z80_card_hit && !mmu_cpu_updating && memory_cycle);
        assign ram_ce0_n = (safe_to_access_ram && !effective_use_rom && active_a11 == 1'b0) ? 1'b0 : 1'b1;
        assign ram_ce1_n = (safe_to_access_ram && !effective_use_rom && active_a11 == 1'b1) ? 1'b0 : 1'b1;

        wire [7:0] rom_atl_data  = dma_is_active ? dma_phys_addr[18:11] : {3'b000, z80_addr[15:11]};
        
        wire [7:0] z80_atl_intent = mmu_cpu_updating ? l_data : {4'b0000, z80_addr[15:12]};
                                                          
        wire [7:0] ram_atl_data  = dma_is_active ? dma_phys_addr[19:12] : z80_atl_intent;
        wire [7:0] final_atl_out = effective_use_rom ? rom_atl_data : ram_atl_data;
    `else
        // Clean Hardware
        assign l_addr = dma_is_active ? dma_phys_addr[11:0] : z80_addr[11:0];
        wire bank_select = atl_data[7];
        
        wire safe_to_access_ram = dma_is_active || (internal_z80_card_hit && !mmu_cpu_updating && memory_cycle);
        assign ram_ce0_n = (safe_to_access_ram && !effective_use_rom && bank_select == 1'b0) ? 1'b0 : 1'b1;
        assign ram_ce1_n = (safe_to_access_ram && !effective_use_rom && bank_select == 1'b1) ? 1'b0 : 1'b1;

        wire [7:0] z80_atl_intent = mmu_cpu_updating ? l_data : {4'b0000, z80_addr[15:12]};

        wire [7:0] final_atl_out = dma_is_active ? dma_phys_addr[19:12] : z80_atl_intent;
    `endif

    assign atl_data = atl_drive_en ? final_atl_out : 8'hzz;

    wire active_write = dma_is_active ? !dma_local_we_n : (z80_grant && !z80_wr_n);
    assign rom_ce_n  = (safe_to_access_ram && effective_use_rom && !active_write) ? 1'b0 : 1'b1;
    assign ram_oe_n = dma_is_active ? dma_local_oe_n : (z80_grant ? z80_rd_n : 1'b1);
    assign ram_we_n = effective_use_rom ? 1'b1 : (dma_is_active ? dma_local_we_n : (z80_grant ? z80_wr_n : 1'b1));

    wire [7:0] interrupt_vector = 8'h40 | latched_id; 
    assign l_data = responding_to_intack ? interrupt_vector : 8'hzz;

    // ==========================================
    // 6. CYCLE STEALING: INTERCEPT & OVERRIDE LOGIC
    // ==========================================
    assign z80_wait_n = ((arbiter_hit && dma_is_active) || arbiter_wait_n == 1'b0) ? 1'b0 : 1'bz;
    //assign sh_c_dir = dma_is_active ? (!dma_local_oe_n) : dma_internal_sh_c_dir;
   assign sh_c_dir = dma_is_master ? 1'b0 : 1'b1;

    // assign sh_data_oe_n  = dma_is_active ? 1'b0 : arbiter_sh_data_oe_n;
    assign sh_data_oe_n = arbiter_sh_data_oe_n;

    assign z80_data_oe_n = internal_z80_data_oe_n;
    // assign sh_busy_n = (arbiter_hit && dma_is_active) ? 1'b0 : 1'bz;
    assign sh_busy_n = ((arbiter_hit && dma_is_active) || arbiter_sh_busy_n == 1'b0) ? 1'b0 : 1'bz;
    // assign l_dir = internal_l_dir;
    assign l_dir = (dma_is_active && dma_dir_to_bus) ? 1'b0 : internal_l_dir;

endmodule
