mmosko/Zx50/firmware/FrontPanel_RevA/font.py

# This file contains the 5x7 pixel font data for the HCMS displays.
# Each character is represented by 5 bytes, where each byte is a column
# of pixels. The LSB of the byte is the top-most pixel (Row A).

# ==========================================
# Custom Status Glyphs
# ==========================================
# These are stored at special, non-ASCII character codes.

# --- Z80 Status Glyphs (Full-width blocks) ---
GLYPH_UPPER_BLOCK = 0x01  # ▀ (Top 3 rows: A, B, C)
GLYPH_LOWER_BLOCK = 0x02  # ▄ (Bottom 3 rows: E, F, G)
GLYPH_FULL_BLOCK  = 0x03  # █ (All rows)

# --- Shadow Bus Quadrant Glyphs (2x3 blocks) ---
GLYPH_QUAD_UL      = 0x04 # Upper-Left
GLYPH_QUAD_UR      = 0x05 # Upper-Right
GLYPH_QUAD_LL      = 0x06 # Lower-Left
GLYPH_QUAD_LR      = 0x07 # Lower-Right
GLYPH_QUAD_UL_UR   = 0x08 # UL + UR
GLYPH_QUAD_UL_LL   = 0x09 # UL + LL
GLYPH_QUAD_UL_LR   = 0x0A # UL + LR
GLYPH_QUAD_UR_LR   = 0x0B # UR + LR
GLYPH_QUAD_LL_UR   = 0x0C # LL + UR
GLYPH_QUAD_LL_LR   = 0x0D # LL + LR
GLYPH_QUAD_UL_LL_UR = 0x0E # UL + LL + UR
GLYPH_QUAD_UL_LL_LR = 0x0F # UL + LL + LR
GLYPH_QUAD_UL_UR_LR = 0x10 # UL + UR + LR
GLYPH_QUAD_LL_UR_LR = 0x11 # LL + UR + LR
GLYPH_QUAD_ALL      = 0x12 # All four quadrants

# Font data map, mapping a character code to a tuple of 5 bytes.
FONT_MAP = {
    # --- Custom Glyphs ---
    0x00: (0x00, 0x00, 0x00, 0x00, 0x00), # Space

    # --- Type 1: tatus Glyphs (Full 5-pixel-wide horizontal bars) ---
    GLYPH_UPPER_BLOCK: (0x07, 0x07, 0x07, 0x07, 0x07),  # ▀ Top 3 rows across all columns
    GLYPH_LOWER_BLOCK: (0x70, 0x70, 0x70, 0x70, 0x70),  # ▄ Bottom 3 rows across all columns
    GLYPH_FULL_BLOCK: (0x7F, 0x7F, 0x7F, 0x7F, 0x7F),  # █ All 7 rows across all columns

    # --- Type 2: Quadrant Glyphs (2x3 blocks with 1-pixel cross margin) ---
    # Single Quadrants
    GLYPH_QUAD_UL: (0x07, 0x07, 0x00, 0x00, 0x00),  # Upper-Left only
    GLYPH_QUAD_UR: (0x00, 0x00, 0x00, 0x07, 0x07),  # Upper-Right only
    GLYPH_QUAD_LL: (0x70, 0x70, 0x00, 0x00, 0x00),  # Lower-Left only
    GLYPH_QUAD_LR: (0x00, 0x00, 0x00, 0x70, 0x70),  # Lower-Right only

    # Dual Quadrants (Halves)
    GLYPH_QUAD_UL_UR: (0x07, 0x07, 0x00, 0x07, 0x07),  # Top half (both upper blocks)
    GLYPH_QUAD_LL_LR: (0x70, 0x70, 0x00, 0x70, 0x70),  # Bottom half (both lower blocks)
    GLYPH_QUAD_UL_LL: (0x77, 0x77, 0x00, 0x00, 0x00),  # Left half (both left blocks)
    GLYPH_QUAD_UR_LR: (0x00, 0x00, 0x00, 0x77, 0x77),  # Right half (both right blocks)

    # Dual Quadrants (Diagonals)
    GLYPH_QUAD_UL_LR: (0x07, 0x07, 0x00, 0x70, 0x70),  # Diagonal: Upper-Left & Lower-Right
    GLYPH_QUAD_LL_UR: (0x70, 0x70, 0x00, 0x07, 0x07),  # Diagonal: Lower-Left & Upper-Right

    # All Four Quadrants
    GLYPH_QUAD_ALL: (0x77, 0x77, 0x00, 0x77, 0x77),  # All 4 blocks (a window pane shape)

    # --- Standard ASCII ---
    ord(' '): (0x00, 0x00, 0x00, 0x00, 0x00),
    ord('!'): (0x00, 0x00, 0x5f, 0x00, 0x00),
    ord('"'): (0x00, 0x07, 0x00, 0x07, 0x00),
    ord('#'): (0x14, 0x7f, 0x14, 0x7f, 0x14),
    ord('$'): (0x24, 0x2a, 0x7f, 0x2a, 0x12),
    ord('%'): (0x23, 0x13, 0x08, 0x64, 0x62),
    ord('&'): (0x36, 0x49, 0x55, 0x22, 0x50),
    ord("'"): (0x00, 0x05, 0x03, 0x00, 0x00),
    ord('('): (0x00, 0x1c, 0x22, 0x41, 0x00),
    ord(')'): (0x00, 0x41, 0x22, 0x1c, 0x00),
    ord('*'): (0x14, 0x08, 0x3e, 0x08, 0x14),
    ord('+'): (0x08, 0x08, 0x3e, 0x08, 0x08),
    ord(','): (0x00, 0x50, 0x30, 0x00, 0x00),
    ord('-'): (0x08, 0x08, 0x08, 0x08, 0x08),
    ord('.'): (0x00, 0x60, 0x60, 0x00, 0x00),
    ord('/'): (0x20, 0x10, 0x08, 0x04, 0x02),
    ord('0'): (0x3e, 0x51, 0x49, 0x45, 0x3e),
    ord('1'): (0x00, 0x42, 0x7f, 0x40, 0x00),
    ord('2'): (0x42, 0x61, 0x51, 0x49, 0x46),
    ord('3'): (0x21, 0x41, 0x45, 0x4b, 0x31),
    ord('4'): (0x18, 0x14, 0x12, 0x7f, 0x10),
    ord('5'): (0x27, 0x45, 0x45, 0x45, 0x39),
    ord('6'): (0x3c, 0x4a, 0x49, 0x49, 0x30),
    ord('7'): (0x01, 0x71, 0x09, 0x05, 0x03),
    ord('8'): (0x36, 0x49, 0x49, 0x49, 0x36),
    ord('9'): (0x06, 0x49, 0x49, 0x29, 0x1e),
    ord(':'): (0x00, 0x36, 0x36, 0x00, 0x00),
    ord(';'): (0x00, 0x56, 0x36, 0x00, 0x00),
    ord('<'): (0x08, 0x14, 0x22, 0x41, 0x00),
    ord('='): (0x14, 0x14, 0x14, 0x14, 0x14),
    ord('>'): (0x00, 0x41, 0x22, 0x14, 0x08),
    ord('?'): (0x02, 0x01, 0x51, 0x09, 0x06),
    ord('@'): (0x32, 0x49, 0x79, 0x41, 0x3e),
    ord('A'): (0x7e, 0x11, 0x11, 0x11, 0x7e),
    ord('B'): (0x7f, 0x49, 0x49, 0x49, 0x36),
    ord('C'): (0x3e, 0x41, 0x41, 0x41, 0x22),
    ord('D'): (0x7f, 0x41, 0x41, 0x22, 0x1c),
    ord('E'): (0x7f, 0x49, 0x49, 0x49, 0x41),
    ord('F'): (0x7f, 0x09, 0x09, 0x09, 0x01),
    ord('G'): (0x3e, 0x41, 0x49, 0x49, 0x7a),
    ord('H'): (0x7f, 0x08, 0x08, 0x08, 0x7f),
    ord('I'): (0x00, 0x41, 0x7f, 0x41, 0x00),
    ord('J'): (0x20, 0x40, 0x41, 0x3f, 0x01),
    ord('K'): (0x7f, 0x08, 0x14, 0x22, 0x41),
    ord('L'): (0x7f, 0x40, 0x40, 0x40, 0x40),
    ord('M'): (0x7f, 0x02, 0x0c, 0x02, 0x7f),
    ord('N'): (0x7f, 0x04, 0x08, 0x10, 0x7f),
    ord('O'): (0x3e, 0x41, 0x41, 0x41, 0x3e),
    ord('P'): (0x7f, 0x09, 0x09, 0x09, 0x06),
    ord('Q'): (0x3e, 0x41, 0x51, 0x21, 0x5e),
    ord('R'): (0x7f, 0x09, 0x19, 0x29, 0x46),
    ord('S'): (0x46, 0x49, 0x49, 0x49, 0x31),
    ord('T'): (0x01, 0x01, 0x7f, 0x01, 0x01),
    ord('U'): (0x3f, 0x40, 0x40, 0x40, 0x3f),
    ord('V'): (0x1f, 0x20, 0x40, 0x20, 0x1f),
    ord('W'): (0x3f, 0x40, 0x38, 0x40, 0x3f),
    ord('X'): (0x63, 0x14, 0x08, 0x14, 0x63),
    ord('Y'): (0x07, 0x08, 0x70, 0x08, 0x07),
    ord('Z'): (0x61, 0x51, 0x49, 0x45, 0x43),
    ord('['): (0x00, 0x7f, 0x41, 0x41, 0x00),
    ord('\\'):(0x02, 0x04, 0x08, 0x10, 0x20),
    ord(']'): (0x00, 0x41, 0x41, 0x7f, 0x00),
    ord('^'): (0x04, 0x02, 0x01, 0x02, 0x04),
    ord('_'): (0x40, 0x40, 0x40, 0x40, 0x40),
    ord('`'): (0x01, 0x02, 0x04, 0x00, 0x00),
    ord('a'): (0x20, 0x54, 0x54, 0x54, 0x78),
    ord('b'): (0x7f, 0x48, 0x48, 0x48, 0x30),
    ord('c'): (0x38, 0x44, 0x44, 0x44, 0x20),
    ord('d'): (0x30, 0x48, 0x48, 0x48, 0x7f),
    ord('e'): (0x38, 0x54, 0x54, 0x54, 0x18),
    ord('f'): (0x08, 0x7e, 0x09, 0x01, 0x02),
    ord('g'): (0x0c, 0x52, 0x52, 0x52, 0x3e),
    ord('h'): (0x7f, 0x08, 0x04, 0x04, 0x78),
    ord('i'): (0x00, 0x44, 0x7d, 0x40, 0x00),
    ord('j'): (0x20, 0x40, 0x44, 0x3d, 0x00),
    ord('k'): (0x7f, 0x10, 0x28, 0x44, 0x00),
    ord('l'): (0x00, 0x41, 0x7f, 0x40, 0x00),
    ord('m'): (0x7c, 0x04, 0x18, 0x04, 0x78),
    ord('n'): (0x7c, 0x08, 0x04, 0x04, 0x78),
    ord('o'): (0x38, 0x44, 0x44, 0x44, 0x38),
    ord('p'): (0x7c, 0x14, 0x14, 0x14, 0x08),
    ord('q'): (0x08, 0x14, 0x14, 0x14, 0x7c),
    ord('r'): (0x7c, 0x08, 0x04, 0x04, 0x08),
    ord('s'): (0x48, 0x54, 0x54, 0x54, 0x20),
    ord('t'): (0x04, 0x3f, 0x44, 0x40, 0x20),
    ord('u'): (0x3c, 0x40, 0x40, 0x20, 0x7c),
    ord('v'): (0x1c, 0x20, 0x40, 0x20, 0x1c),
    ord('w'): (0x3c, 0x40, 0x30, 0x40, 0x3c),
    ord('x'): (0x44, 0x28, 0x10, 0x28, 0x44),
    ord('y'): (0x0c, 0x50, 0x50, 0x50, 0x3c),
    ord('z'): (0x44, 0x64, 0x54, 0x4c, 0x44),
    ord('{'): (0x08, 0x14, 0x22, 0x22, 0x14),
    ord('|'): (0x00, 0x00, 0x7f, 0x00, 0x00),
    ord('}'): (0x14, 0x22, 0x22, 0x14, 0x08),
    ord('~'): (0x08, 0x08, 0x08, 0x08, 0x00)
}
